wyolum/ultim8x8/kicad/ultim8x8_data/adafruit_products_M0_2796_pinout_v1_0.png

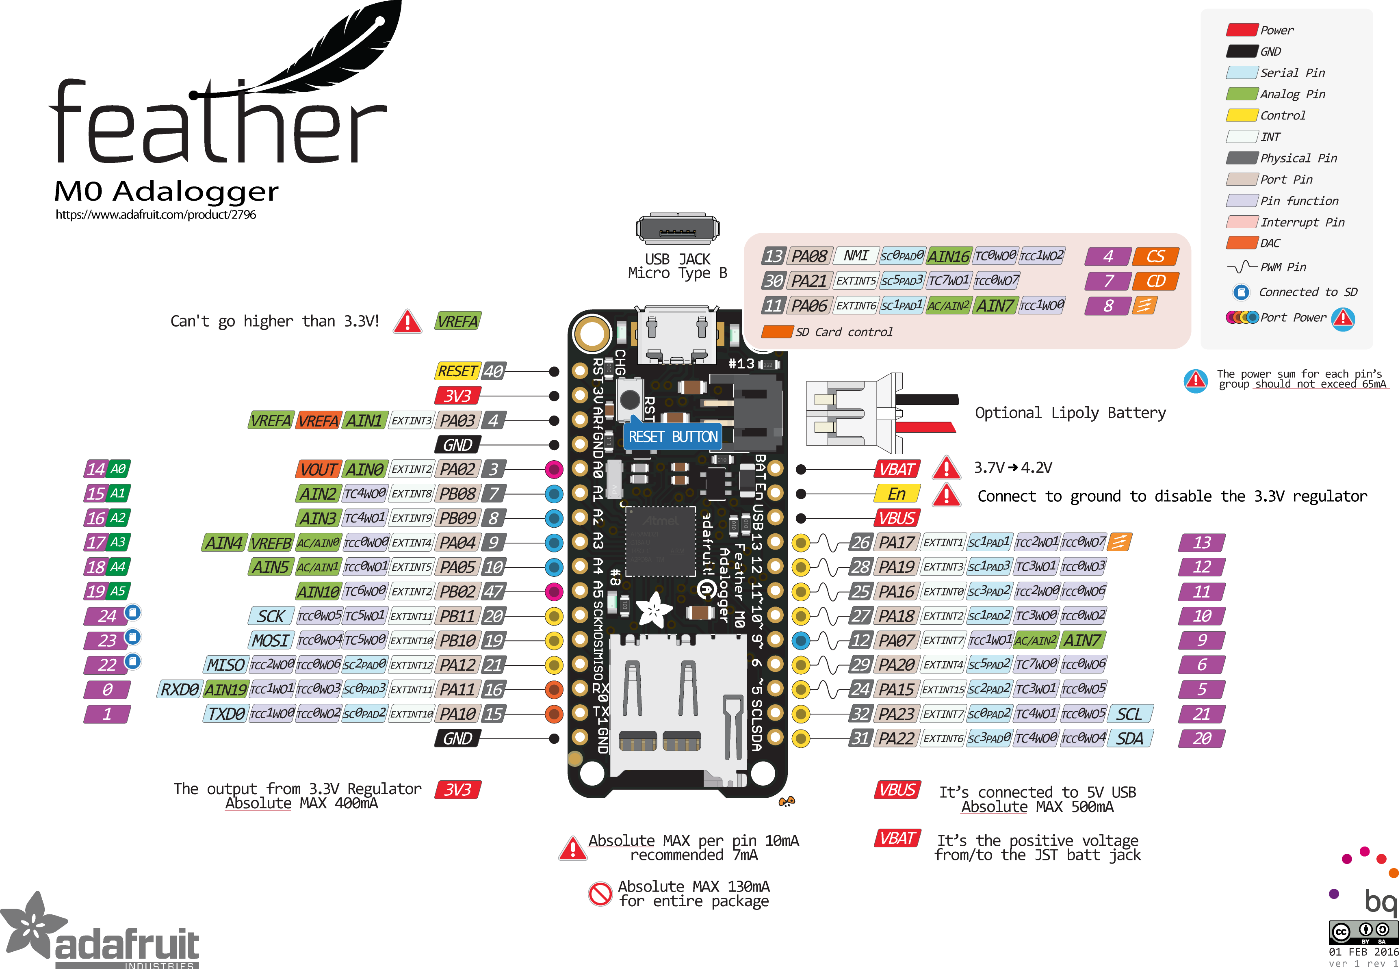
kicad/ultim8x8_data/adafruit_products_M0_2796_pinout_v1_0.png
