wyolum/ultim8x8/kicad/ultim8x8_data/wyolum_butterfly.png

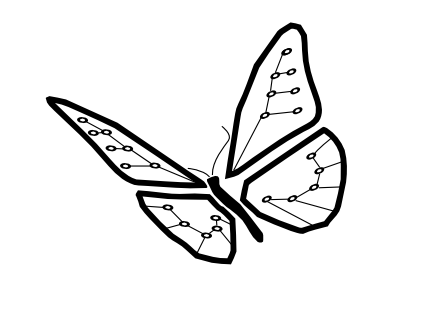
kicad/ultim8x8_data/wyolum_butterfly.png
