wyolum/ultim8x8/kicad/ultim_8x8_v2/ultim8x8_images/ultim8x8_06.png

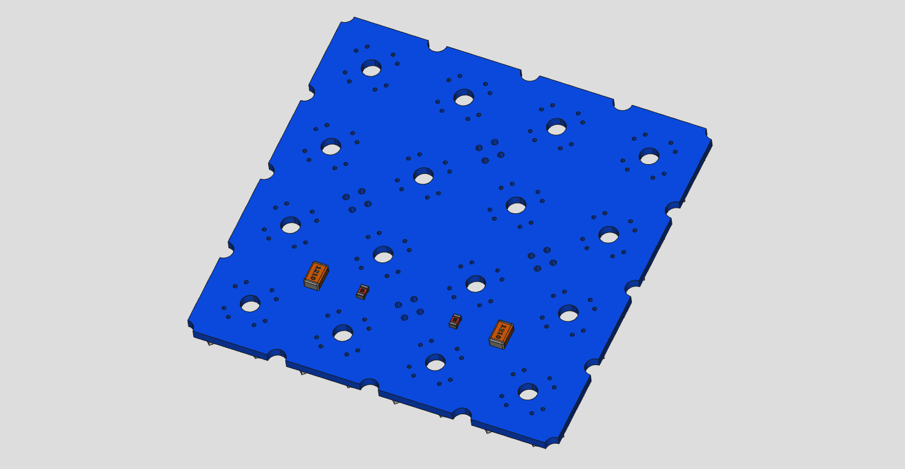
kicad/ultim_8x8_v2/ultim8x8_images/ultim8x8_06.png
