wyolum/ultim8x8/kicad/ultim_8x8_v2/ultim8x8_images/v1/ultim8x8_01.png

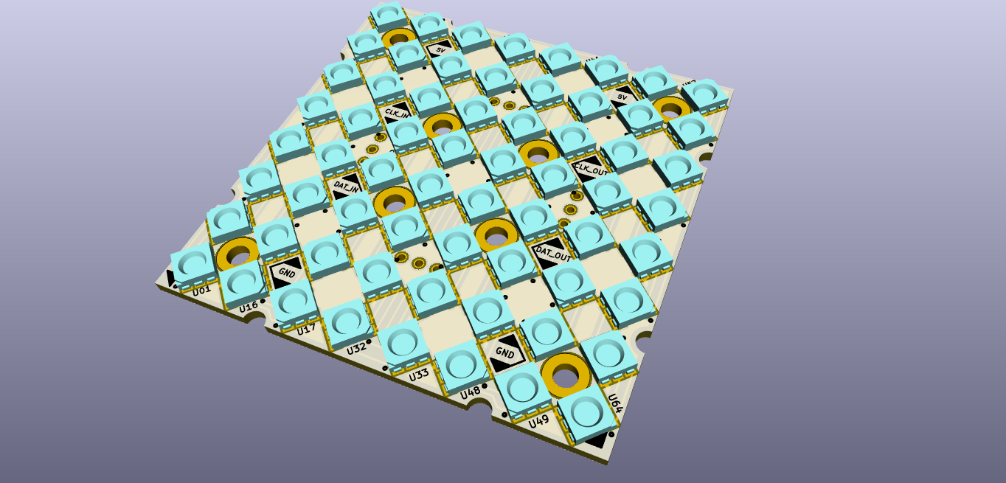
kicad/ultim_8x8_v2/ultim8x8_images/v1/ultim8x8_01.png
