wyolum/ultim8x8/kicad/ultim_bus_conn/ultim_bus_conn_images/ultim_bus_conn_02.png

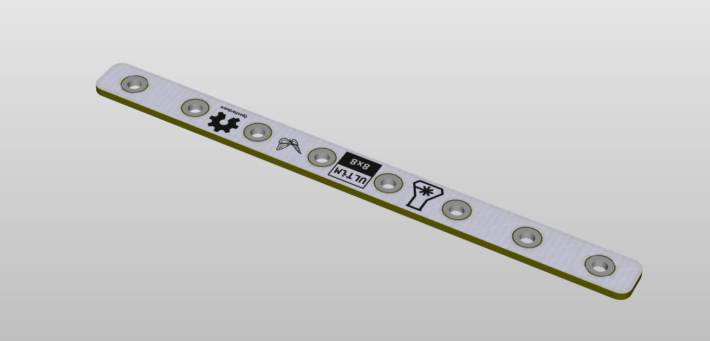
kicad/ultim_bus_conn/ultim_bus_conn_images/ultim_bus_conn_02.png
