wyolum/ultim8x8/arduino/DullesNavKey/enclosure/mouting_guide.stl

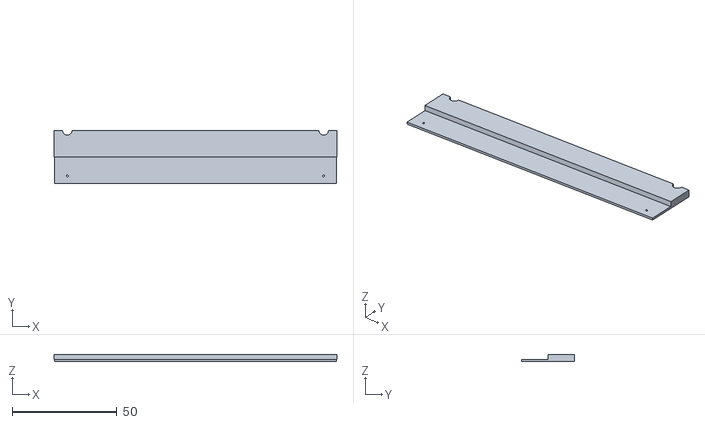
[picture p50: CAD file, 2019-09-12]
arduino/DullesNavKey/enclosure/mouting_guide.stl
135.1 x 25.4 x 3.50
