wyolum/ultim8x8/fabricate/buckle/ultim8x8_feather_buckle_v3.stl

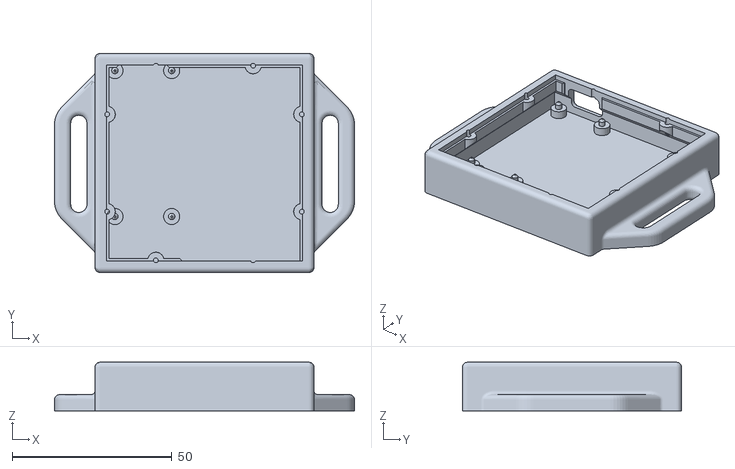
[picture p51: CAD file, 2016-12-25]
fabricate/buckle/ultim8x8_feather_buckle_v3.stl
94.0 x 68.6 x 15.2
