wyolum/ultim8x8/fabricate/STFU/STFU_top.stl

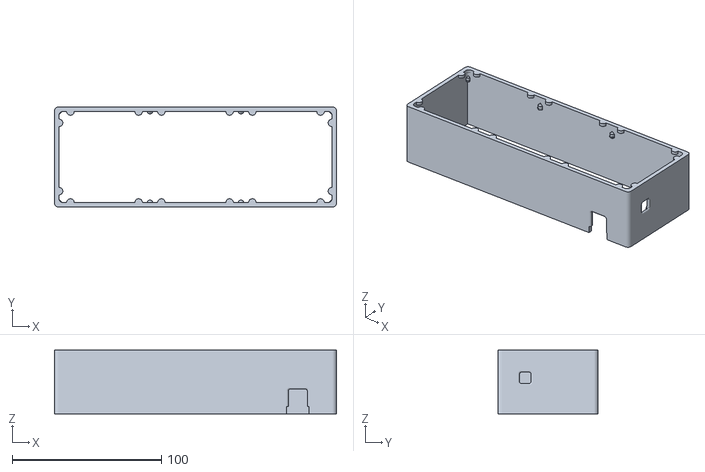
[picture p52: CAD file, 2017-09-21]
fabricate/STFU/STFU_top.stl
189.0 x 67.1 x 42.7
