wyolum/ultim8x8/fabricate/ultim8x_cube01/ultim8x8_cube_face_01.fcstd

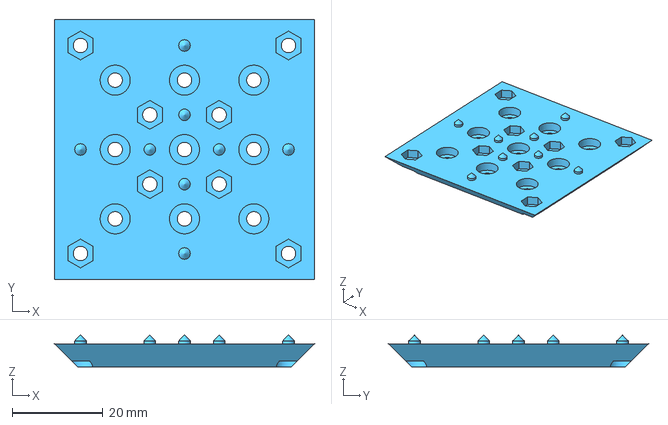
[picture p53: CAD file, 2016-09-29]
fabricate/ultim8x_cube01/ultim8x8_cube_face_01.fcstd
57.1 x 57.1 x 6.99 mm
