wyolum/ultim8x8/fabricate/ultim8x_cube02/cube02_innerface.stl

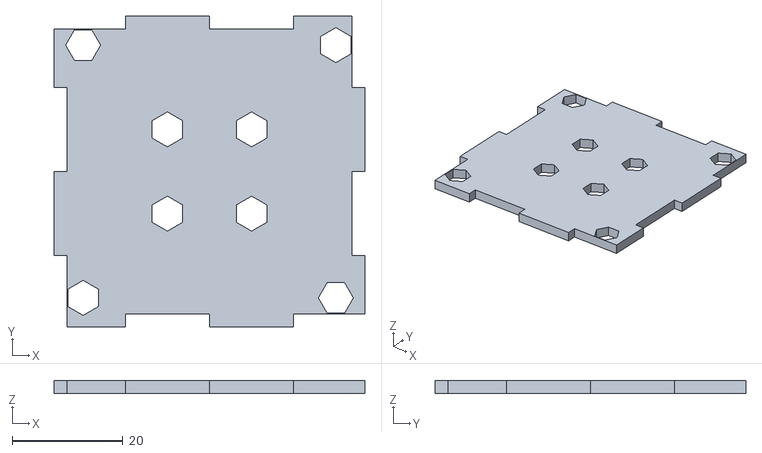
[picture p54: CAD file, 2017-04-09]
fabricate/ultim8x_cube02/cube02_innerface.stl
56.3 x 56.3 x 2.35
