wyolum/ultim8x8/kicad/ultim_8x8_v2/ultim8x8_3D_modules/LED_SMD_APA102_02.step

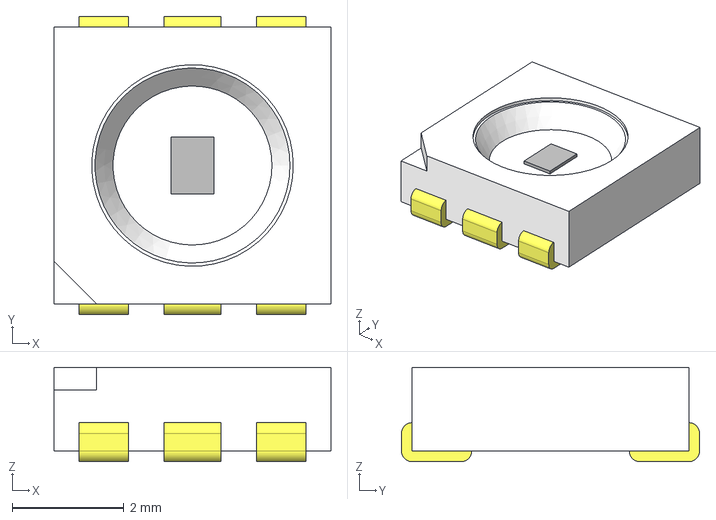
[picture p55: CAD file, 2017-01-15]
kicad/ultim_8x8_v2/ultim8x8_3D_modules/LED_SMD_APA102_02.step
4.95 x 5.33 x 1.69 mm
