wyolum/ultim8x8/kicad/ultim_bus_v5/ultim_bus.FCStd

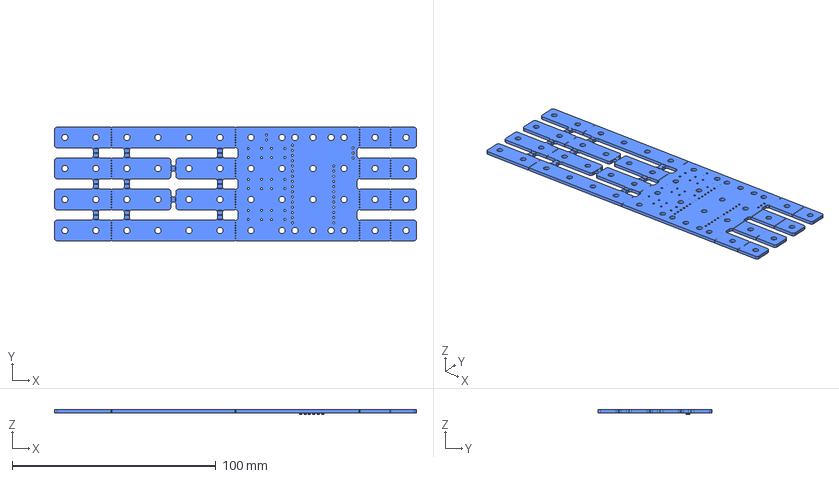
[picture p56: CAD file, 2017-08-31]
kicad/ultim_bus_v5/ultim_bus.FCStd
177.8 x 55.9 x 2.38 mm
Pcb
SW3dPS-0805_SMD_Resistor_
SW3dPS-0805_SMD_Resistor_001
SW3dPS-0805_SMD_Resistor_002
SW3dPS-0805_SMD_Resistor_003
SW3dPS-0805_SMD_Resistor_004
SW3dPS-0805_SMD_Resistor_005
