wyolum/ultim8x8/kicad/ultim_bus_v5/ultim_bus_3dmodules/cap_elco_R100_D200_H460.step

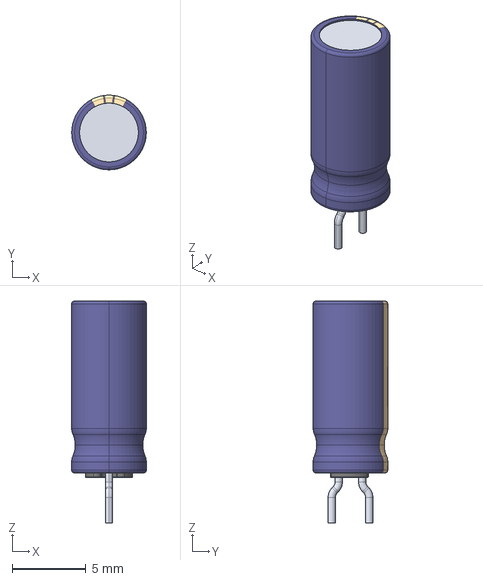
[picture p57: CAD file, 2017-06-14]
kicad/ultim_bus_v5/ultim_bus_3dmodules/cap_elco_R100_D200_H460.step
5.08 x 5.08 x 15.1 mm
