wyolum/ultim8x8/arduino/DullesNavKey/enclosure/hanger.FCStd

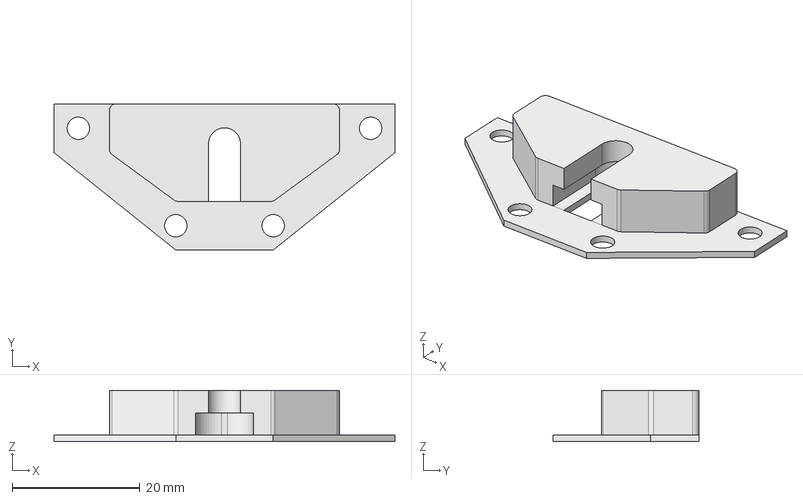
[picture p58: CAD file, 2019-09-02]
arduino/DullesNavKey/enclosure/hanger.FCStd
53.3 x 22.9 x 8.00 mm
