wyolum/ultim8x8/fabricate/STFU/STFU_acrylic.stl

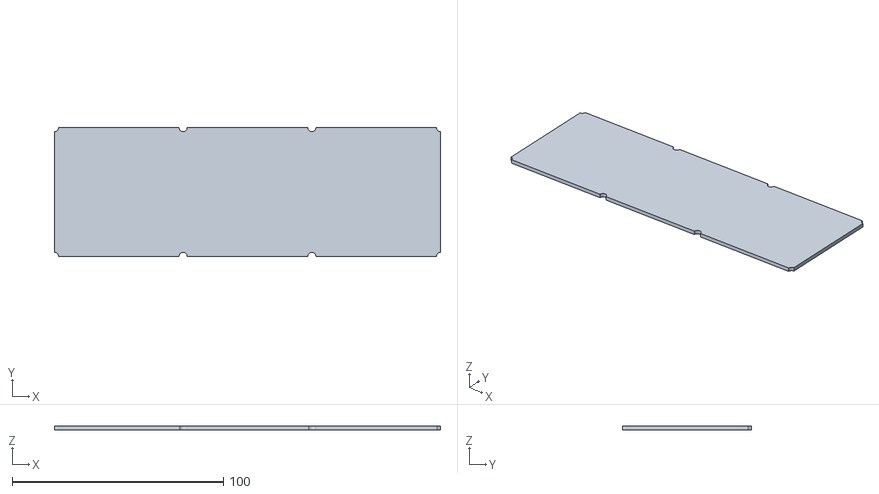
[picture p59: CAD file, 2017-09-21]
fabricate/STFU/STFU_acrylic.stl
182.9 x 61.0 x 2.03
