wyolum/ultim8x8/kicad/ultim_bus_v5/ultim_bus_3dmodules/SW_Switch_SPDT.step

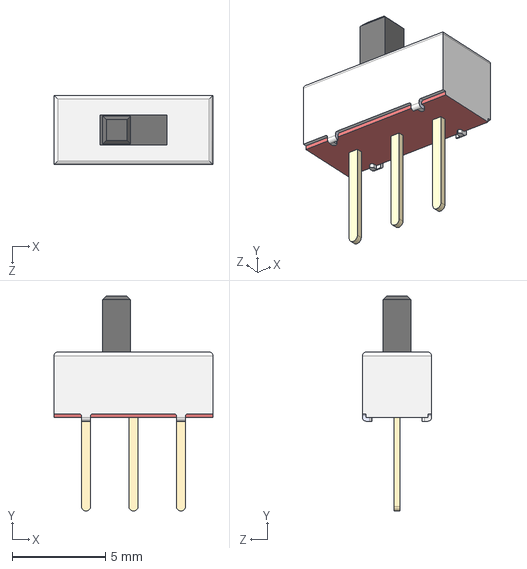
[picture p60: CAD file, 2017-06-14]
kicad/ultim_bus_v5/ultim_bus_3dmodules/SW_Switch_SPDT.step
8.50 x 11.5 x 3.70 mm
