wyolum/ultim8x8/arduino/DesKlok/ClockIOT.stl

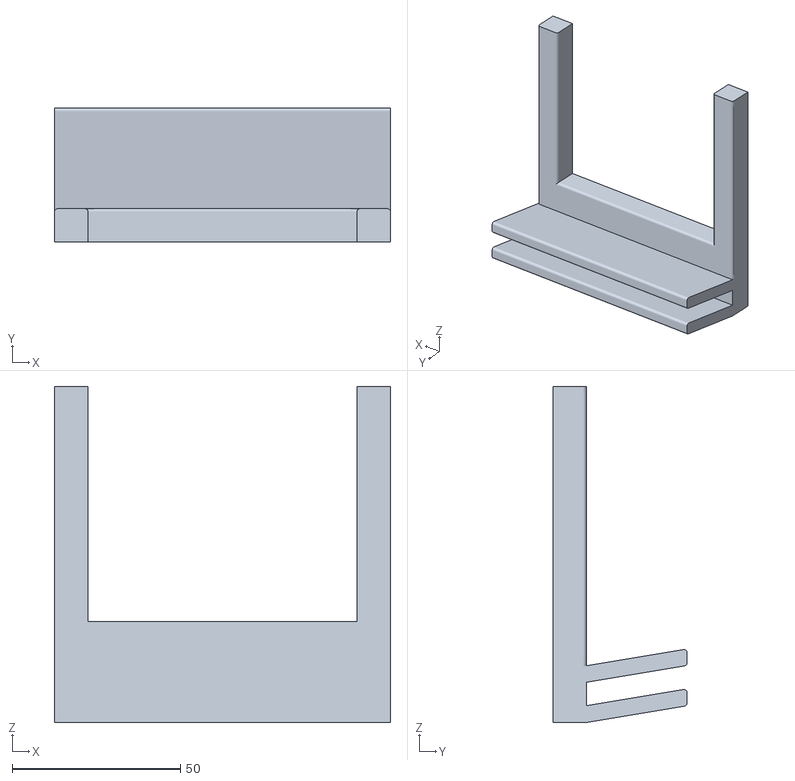
[picture p61: CAD file, 2022-12-24]
arduino/DesKlok/ClockIOT.stl
100.0 x 40.0 x 100.0
