wyolum/ultim8x8/fabricate/ultim8x_cube02/cube02_outerface.stl

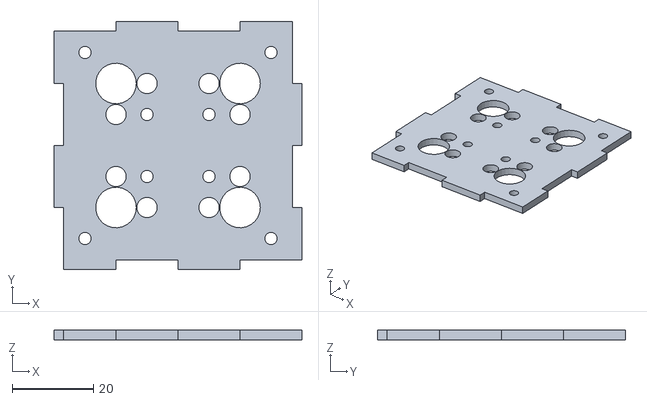
[picture p62: CAD file, 2017-04-09]
fabricate/ultim8x_cube02/cube02_outerface.stl
61.0 x 61.0 x 2.35
