wyolum/ultim8x8/kicad/ultim_bus_v5/ultim_bus_3dmodules/SW_slide_eg1270.step

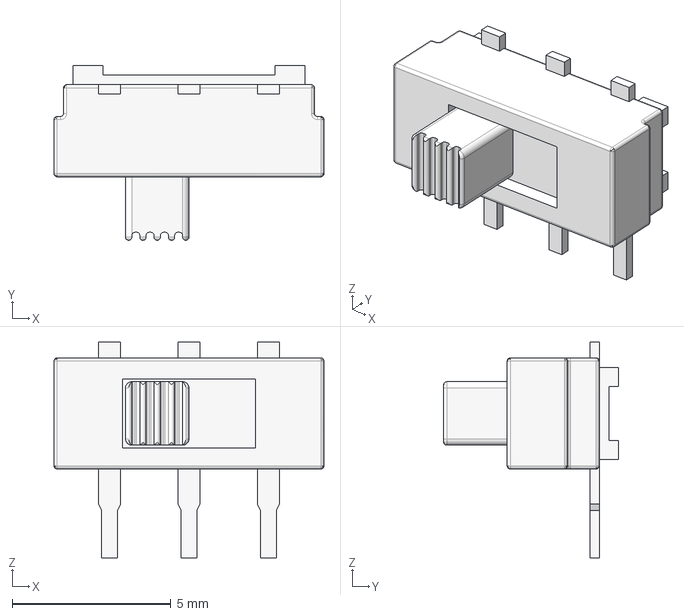
[picture p64: CAD file, 2017-06-14]
kicad/ultim_bus_v5/ultim_bus_3dmodules/SW_slide_eg1270.step
8.50 x 5.50 x 6.80 mm
