wyolum/ultim8x8/fabricate/ultim8x_cube02/cube02_oneface_combined.stl

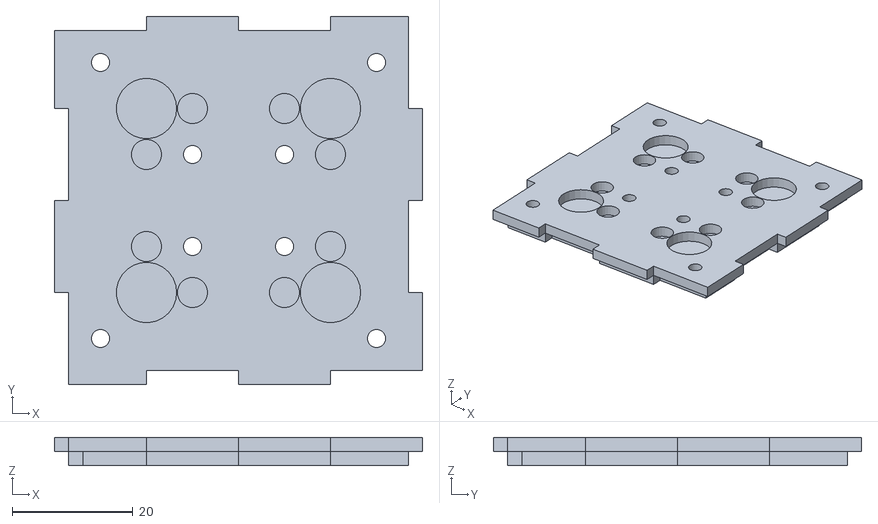
[picture p65: CAD file, 2017-04-09]
fabricate/ultim8x_cube02/cube02_oneface_combined.stl
61.0 x 61.0 x 4.70
