wyolum/ultim8x8/kicad/ultim_8x8_v2/ultim8x8_3D_modules/socket_ra_4pin.step

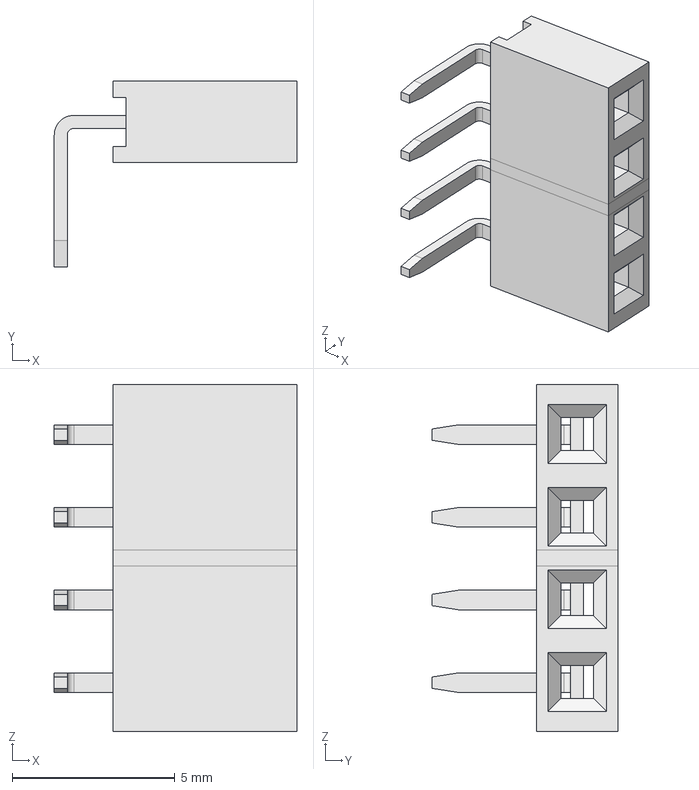
[picture p66: CAD file, 2016-09-08]
kicad/ultim_8x8_v2/ultim8x8_3D_modules/socket_ra_4pin.step
7.45 x 5.70 x 10.7 mm
