wyolum/ultim8x8/kicad/ultim_bus_v5/ultim_bus_3dmodules/r_0805.step

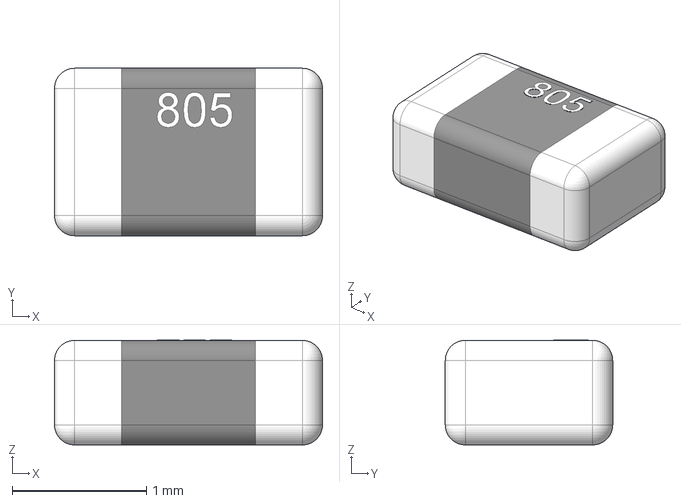
[picture p67: CAD file, 2017-04-03]
kicad/ultim_bus_v5/ultim_bus_3dmodules/r_0805.step
2.00 x 1.25 x 0.782 mm
