wyolum/ultim8x8/kicad/ultim_8x8_v2/ultim8x8_3D_modules/header_1x3_TH_2_54mm.step

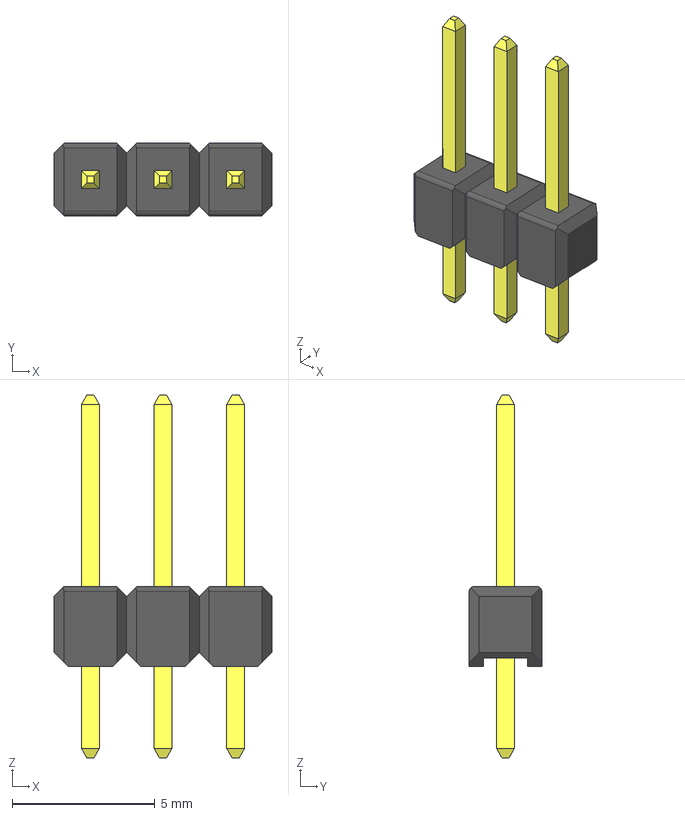
[picture p68: CAD file, 2016-03-18]
kicad/ultim_8x8_v2/ultim8x8_3D_modules/header_1x3_TH_2_54mm.step
7.62 x 2.54 x 12.7 mm
