wyolum/ultim8x8/kicad/ultim_8x8_v2/ultim8x8_3D_modules/cap_1210_3225M.step

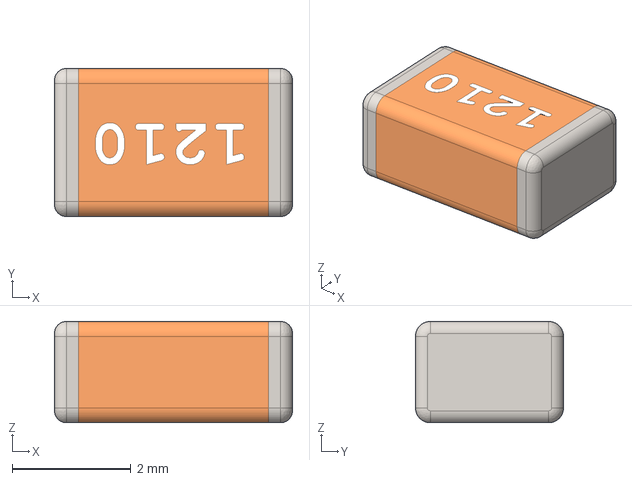
[picture p69: CAD file, 2016-03-18]
kicad/ultim_8x8_v2/ultim8x8_3D_modules/cap_1210_3225M.step
4.00 x 2.49 x 1.70 mm
