wyolum/ultim8x8/kicad/ultim_8x8_v2/ultim8x8_3D_modules/Cap_0805_2012.step

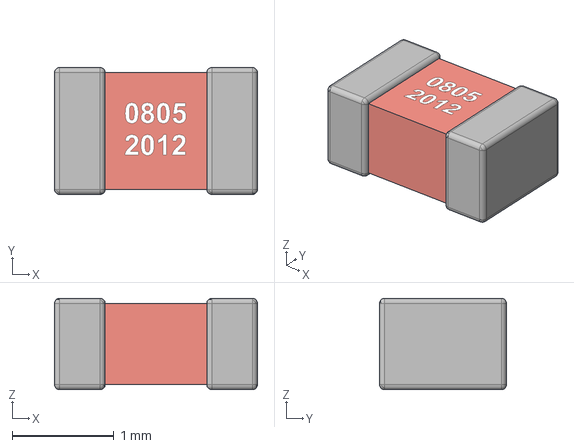
[picture p70: CAD file, 2016-02-18]
kicad/ultim_8x8_v2/ultim8x8_3D_modules/Cap_0805_2012.step
2.00 x 1.25 x 0.9 mm
