wyolum/ultim8x8/kicad/ultim_8x8_v2/ultim8x8_3D_modules/header_Male_RA_Low_3Pin.step

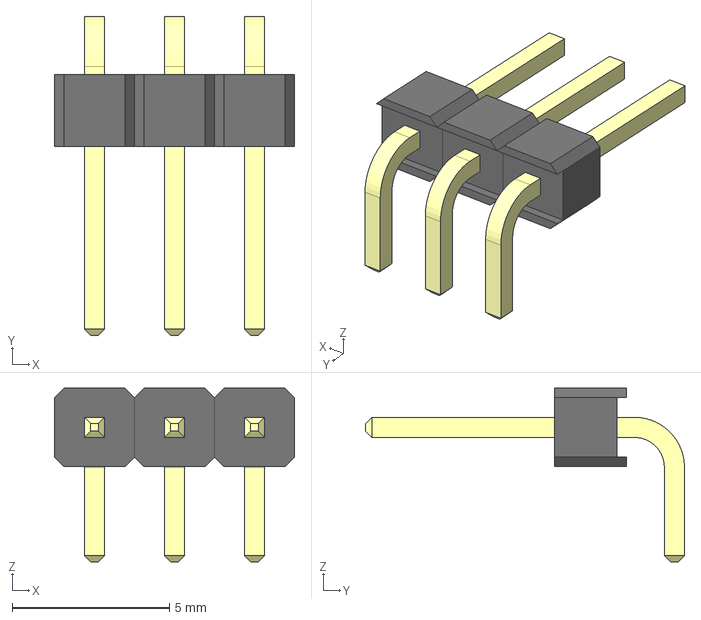
[picture p71: CAD file, 2016-02-18]
kicad/ultim_8x8_v2/ultim8x8_3D_modules/header_Male_RA_Low_3Pin.step
7.62 x 10.1 x 5.52 mm
