wyolum/ultim8x8/fabricate/STFU/SFTU01.png

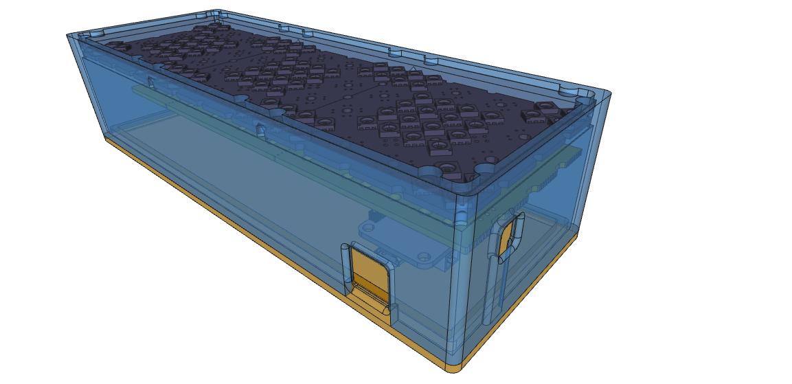
fabricate/STFU/SFTU01.png
