wyolum/ultim8x8/fabricate/STFU/STFU02.png

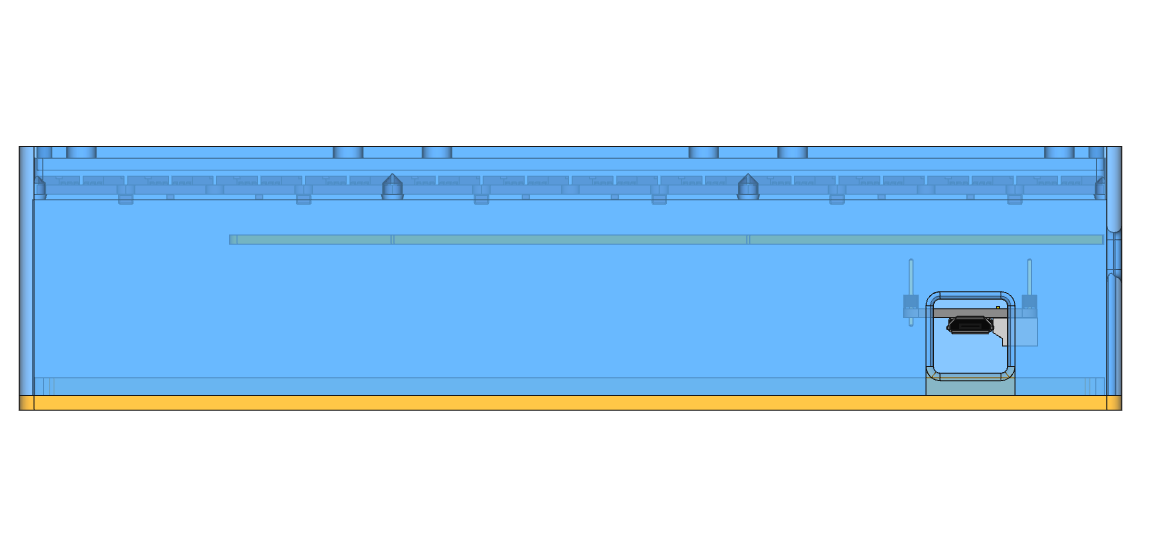
fabricate/STFU/STFU02.png
