wyolum/ultim8x8/fabricate/STFU/STFU03.png

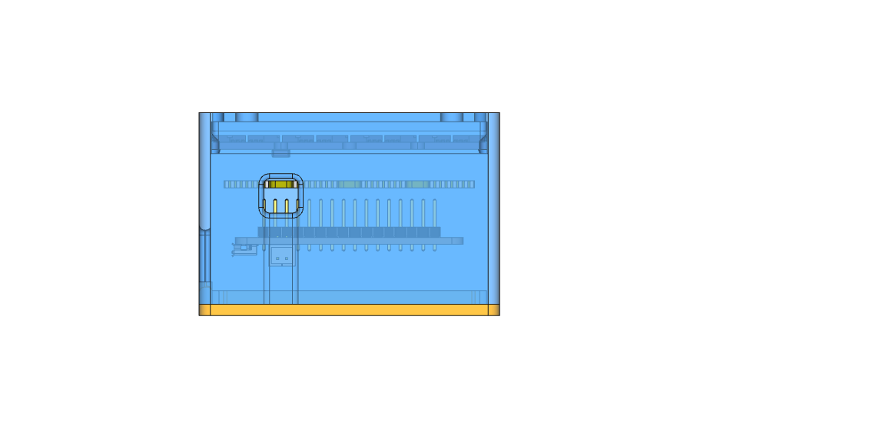
fabricate/STFU/STFU03.png
