wyolum/ultim8x8/fabricate/STFU/STFU04.png

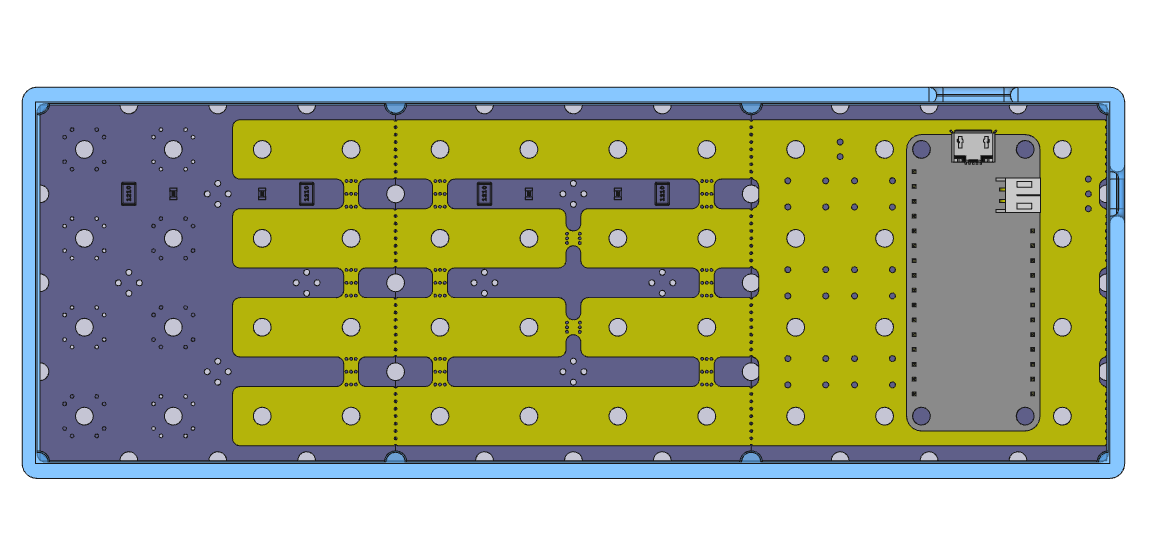
fabricate/STFU/STFU04.png
