wyolum/ultim8x8/fabricate/ultim8x_assy_idea/ultim8x_assy_01.png

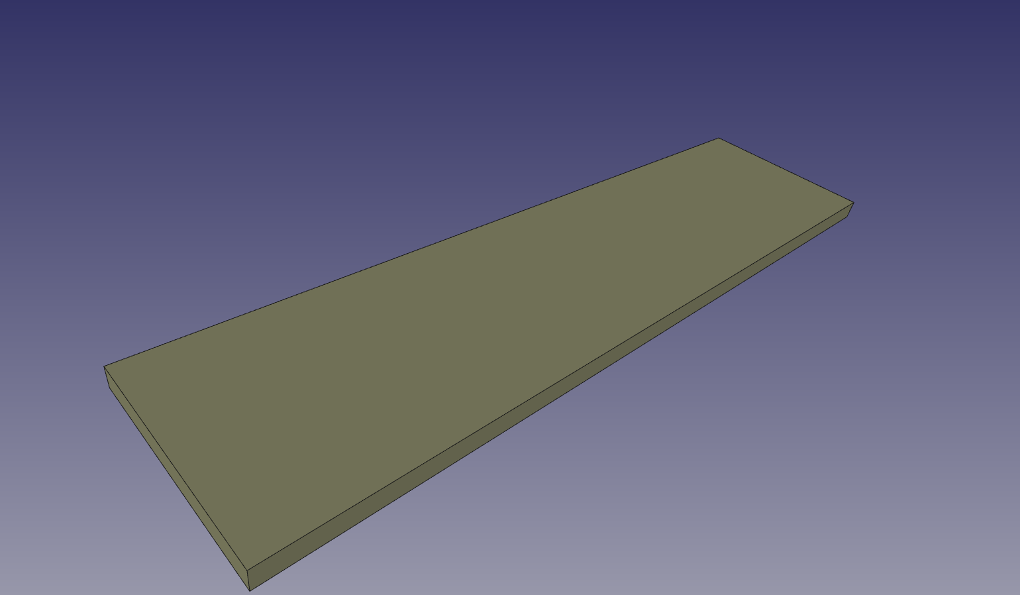
fabricate/ultim8x_assy_idea/ultim8x_assy_01.png
