wyolum/ultim8x8/fabricate/ultim8x_cube01/images/cube01.png

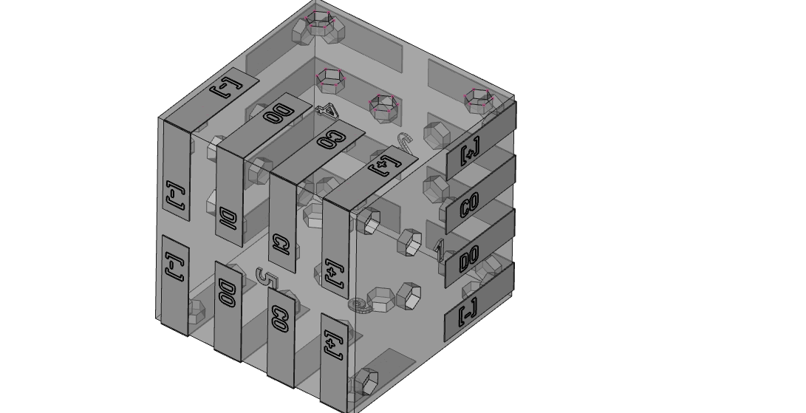
fabricate/ultim8x_cube01/images/cube01.png
