wyolum/ultim8x8/fabricate/ultim8x_cube01/images/cube03.png

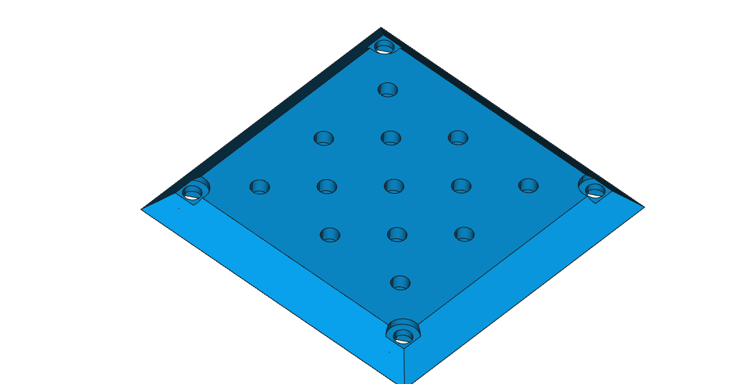
fabricate/ultim8x_cube01/images/cube03.png
