wyolum/ultim8x8/fabricate/ultim8x_cube02/images/cube02_05.png

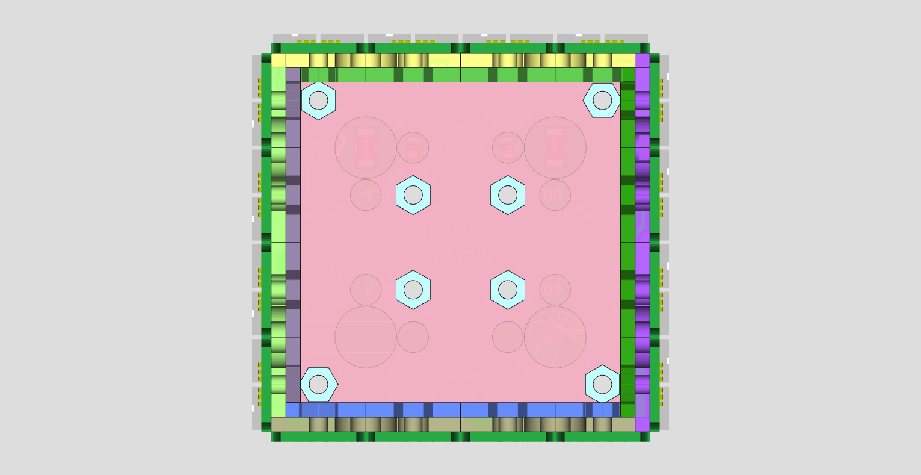
fabricate/ultim8x_cube02/images/cube02_05.png
