wyolum/ultim8x8/kicad/ultim_bus_conn/ultim_bus_conn_pdf/ultim_bus_conn.pdf

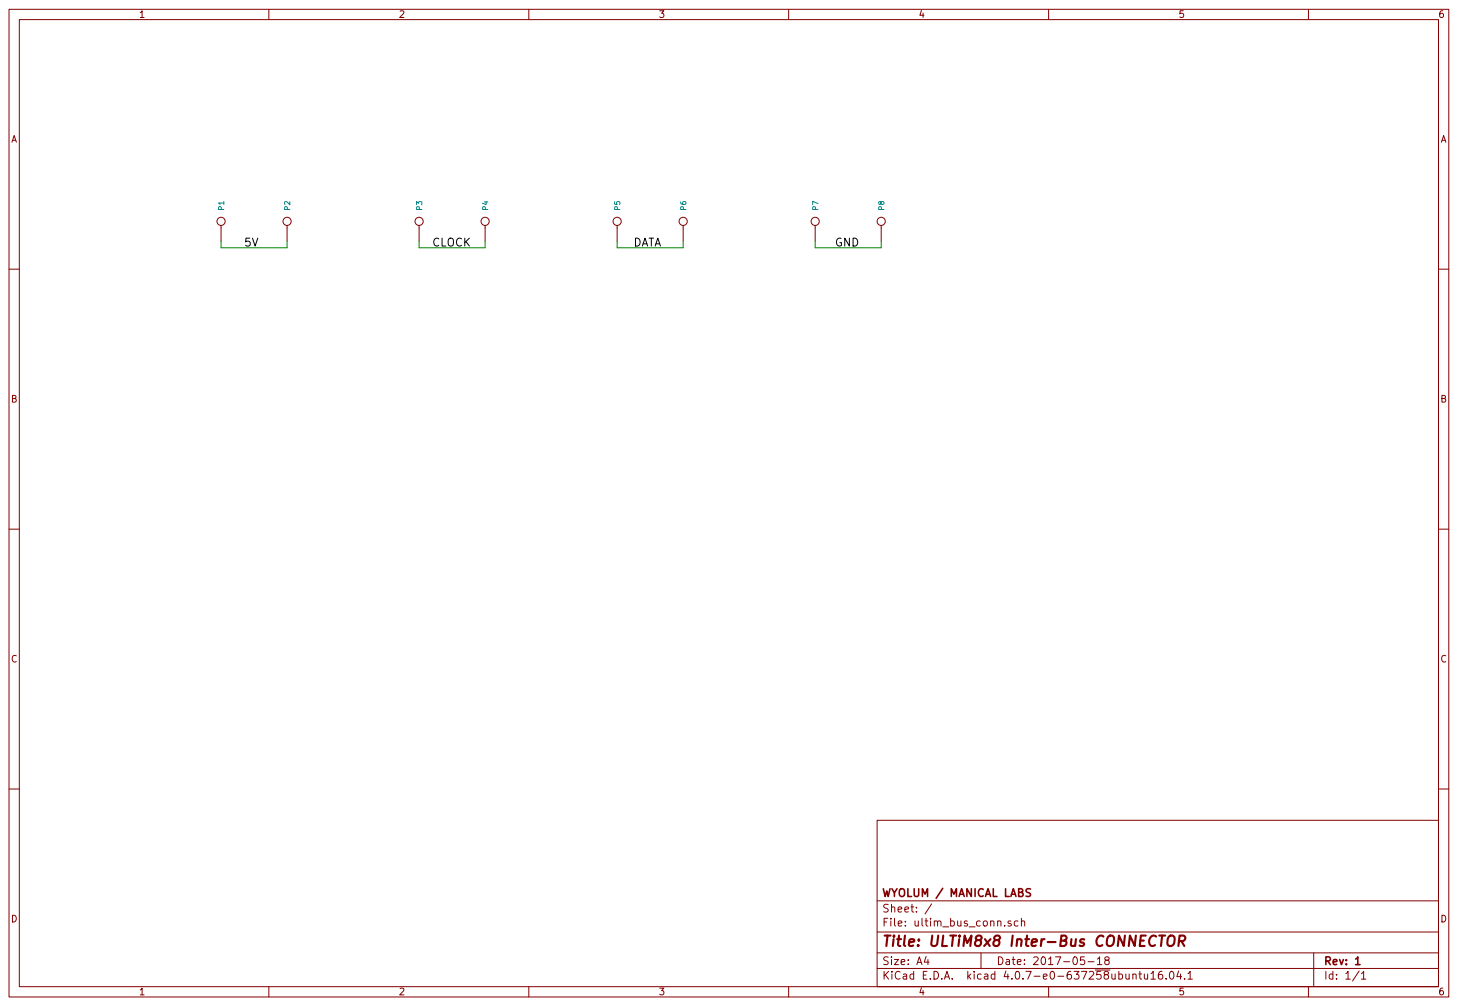
[picture p95: page 1]

Id: 1/1 Title: ULTiM8x8 Inter-Bus CONNECTOR
