wyolum/ultim8x8/kicad/ultim_8x8_v2/ultim8x8_pdf/ultim8x8-B.SilkS.pdf

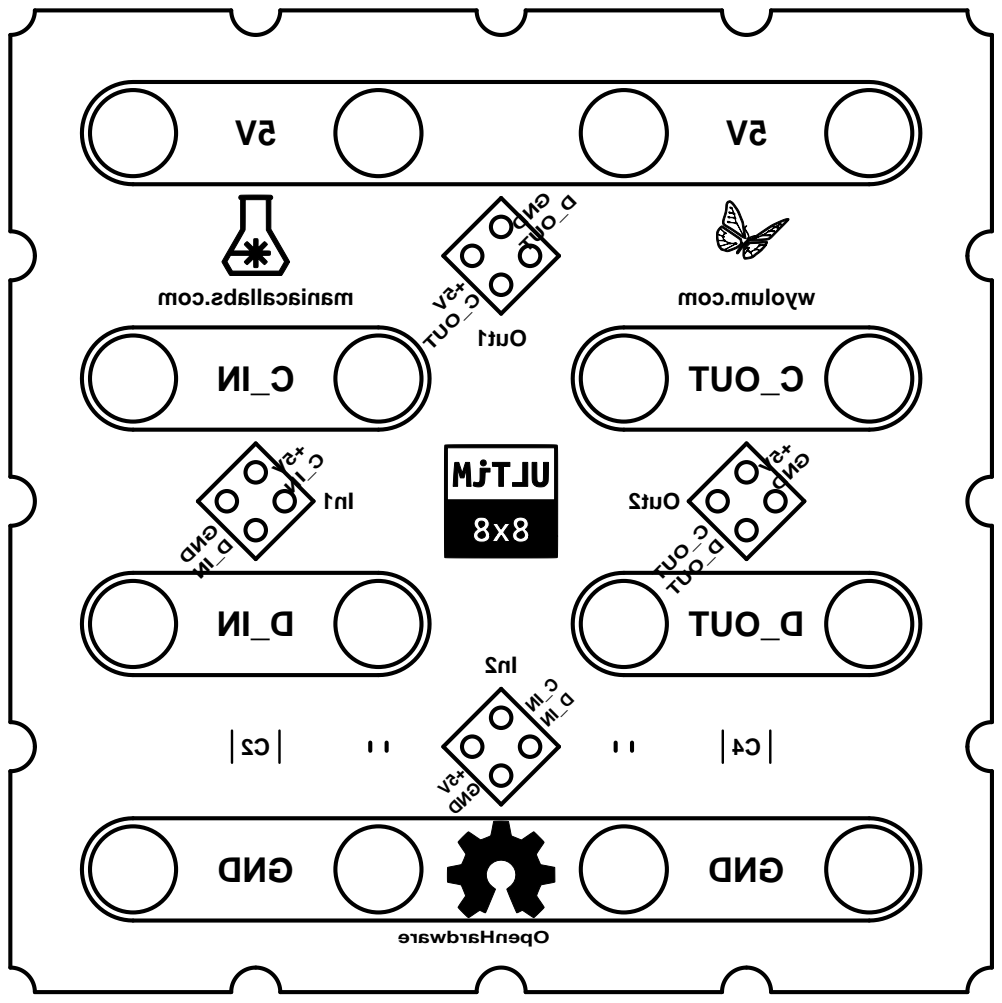
[picture p96: page 1]

File: ultim8x8.kicad_pcb Sheet: WyoManical Labs

Id: 1/1 Title: ultim8x8 RGB LED panel
