wyolum/ultim8x8/kicad/ultim_8x8_v2/ultim8x8_pdf/ultim8x8.pdf

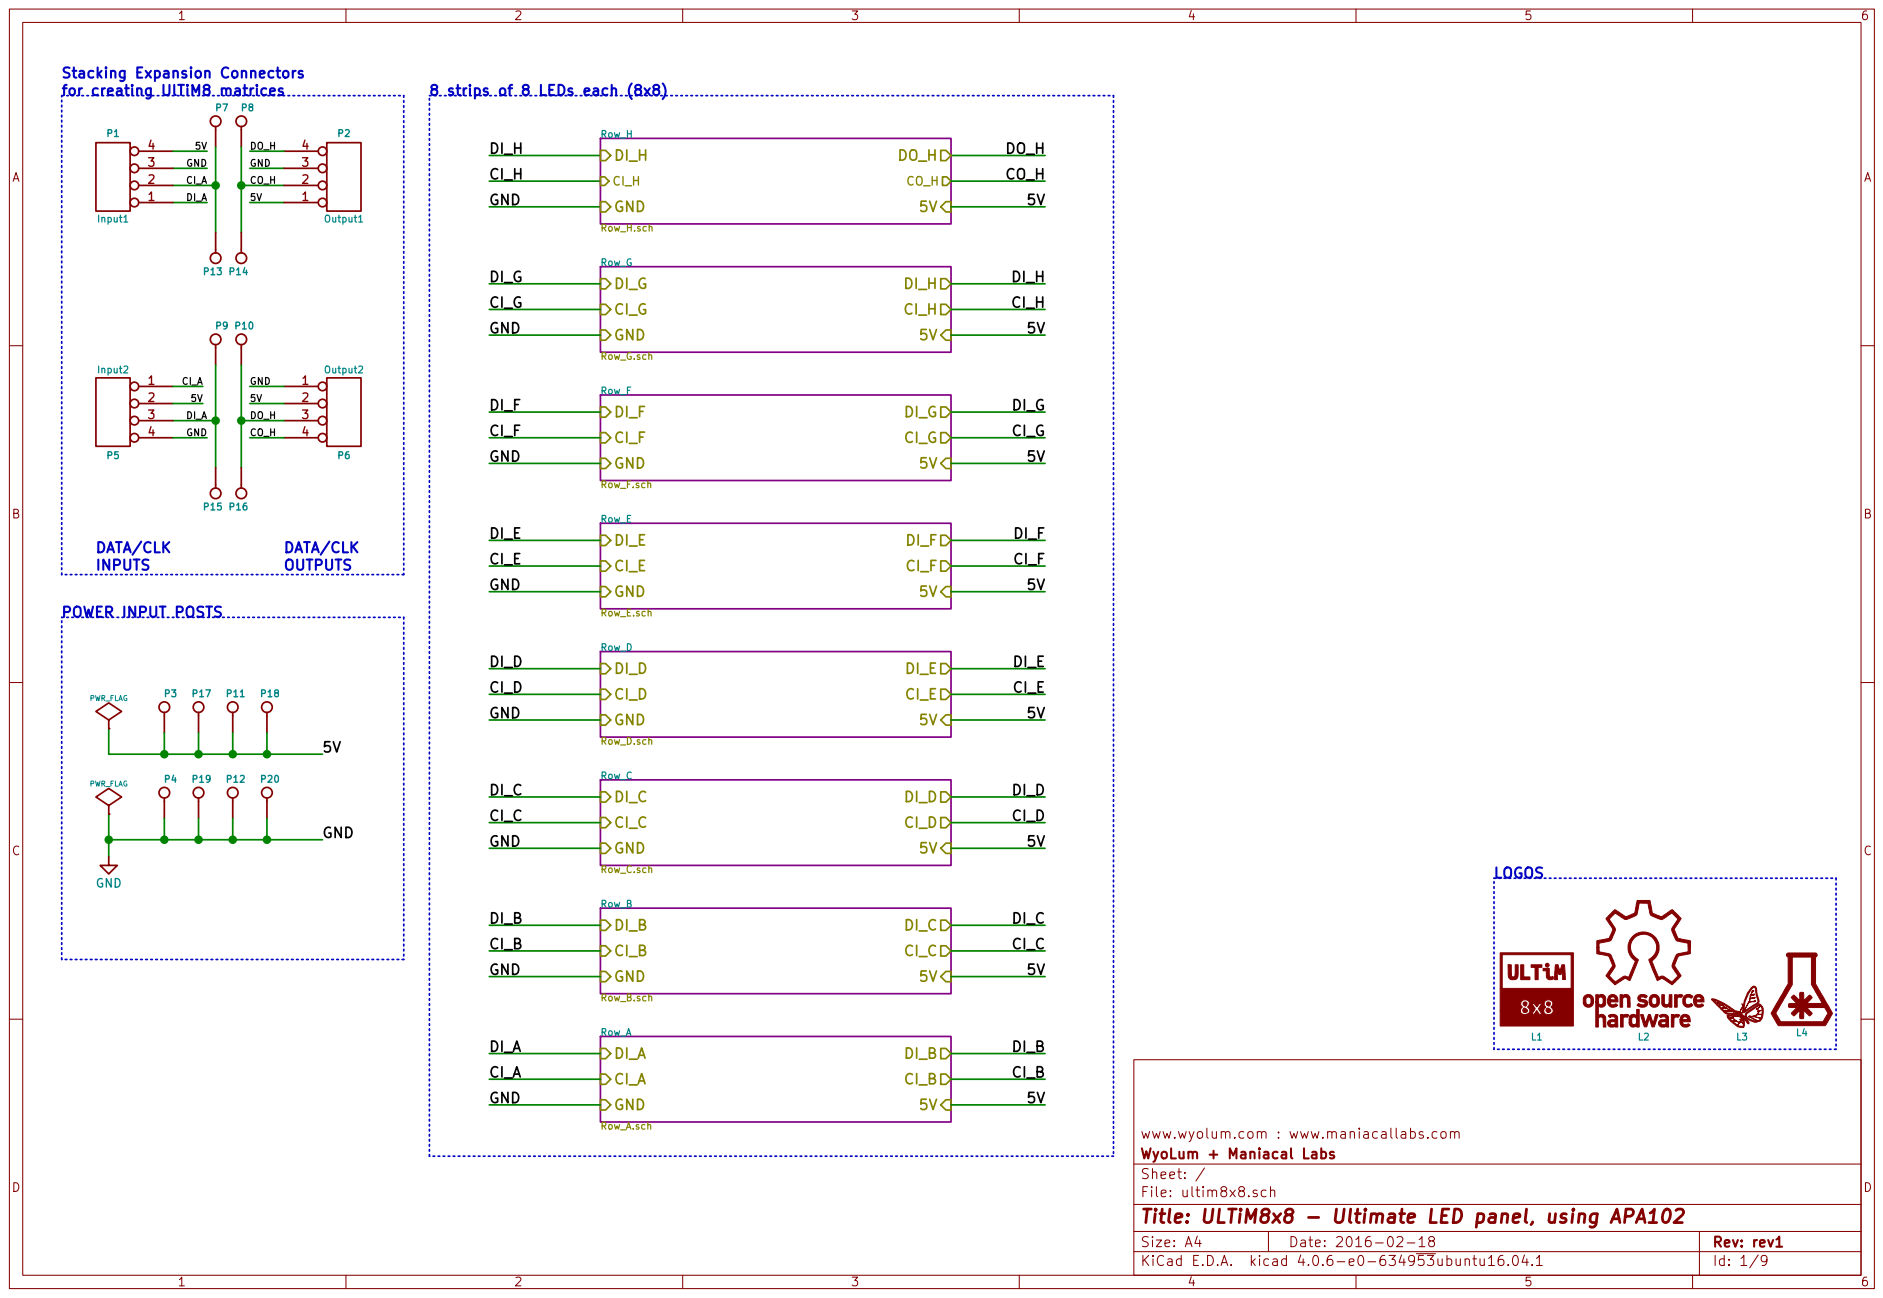
[picture p101: page 1]

8 strips of 8 LEDs each (8x8)

www.wyolum.com : www.maniacallabs.com
File: ultim8x8.sch Sheet: / WyoLum + Maniacal Labs

Id: 1/9 Title: ULTiM8x8 - Ultimate LED panel, using APA102

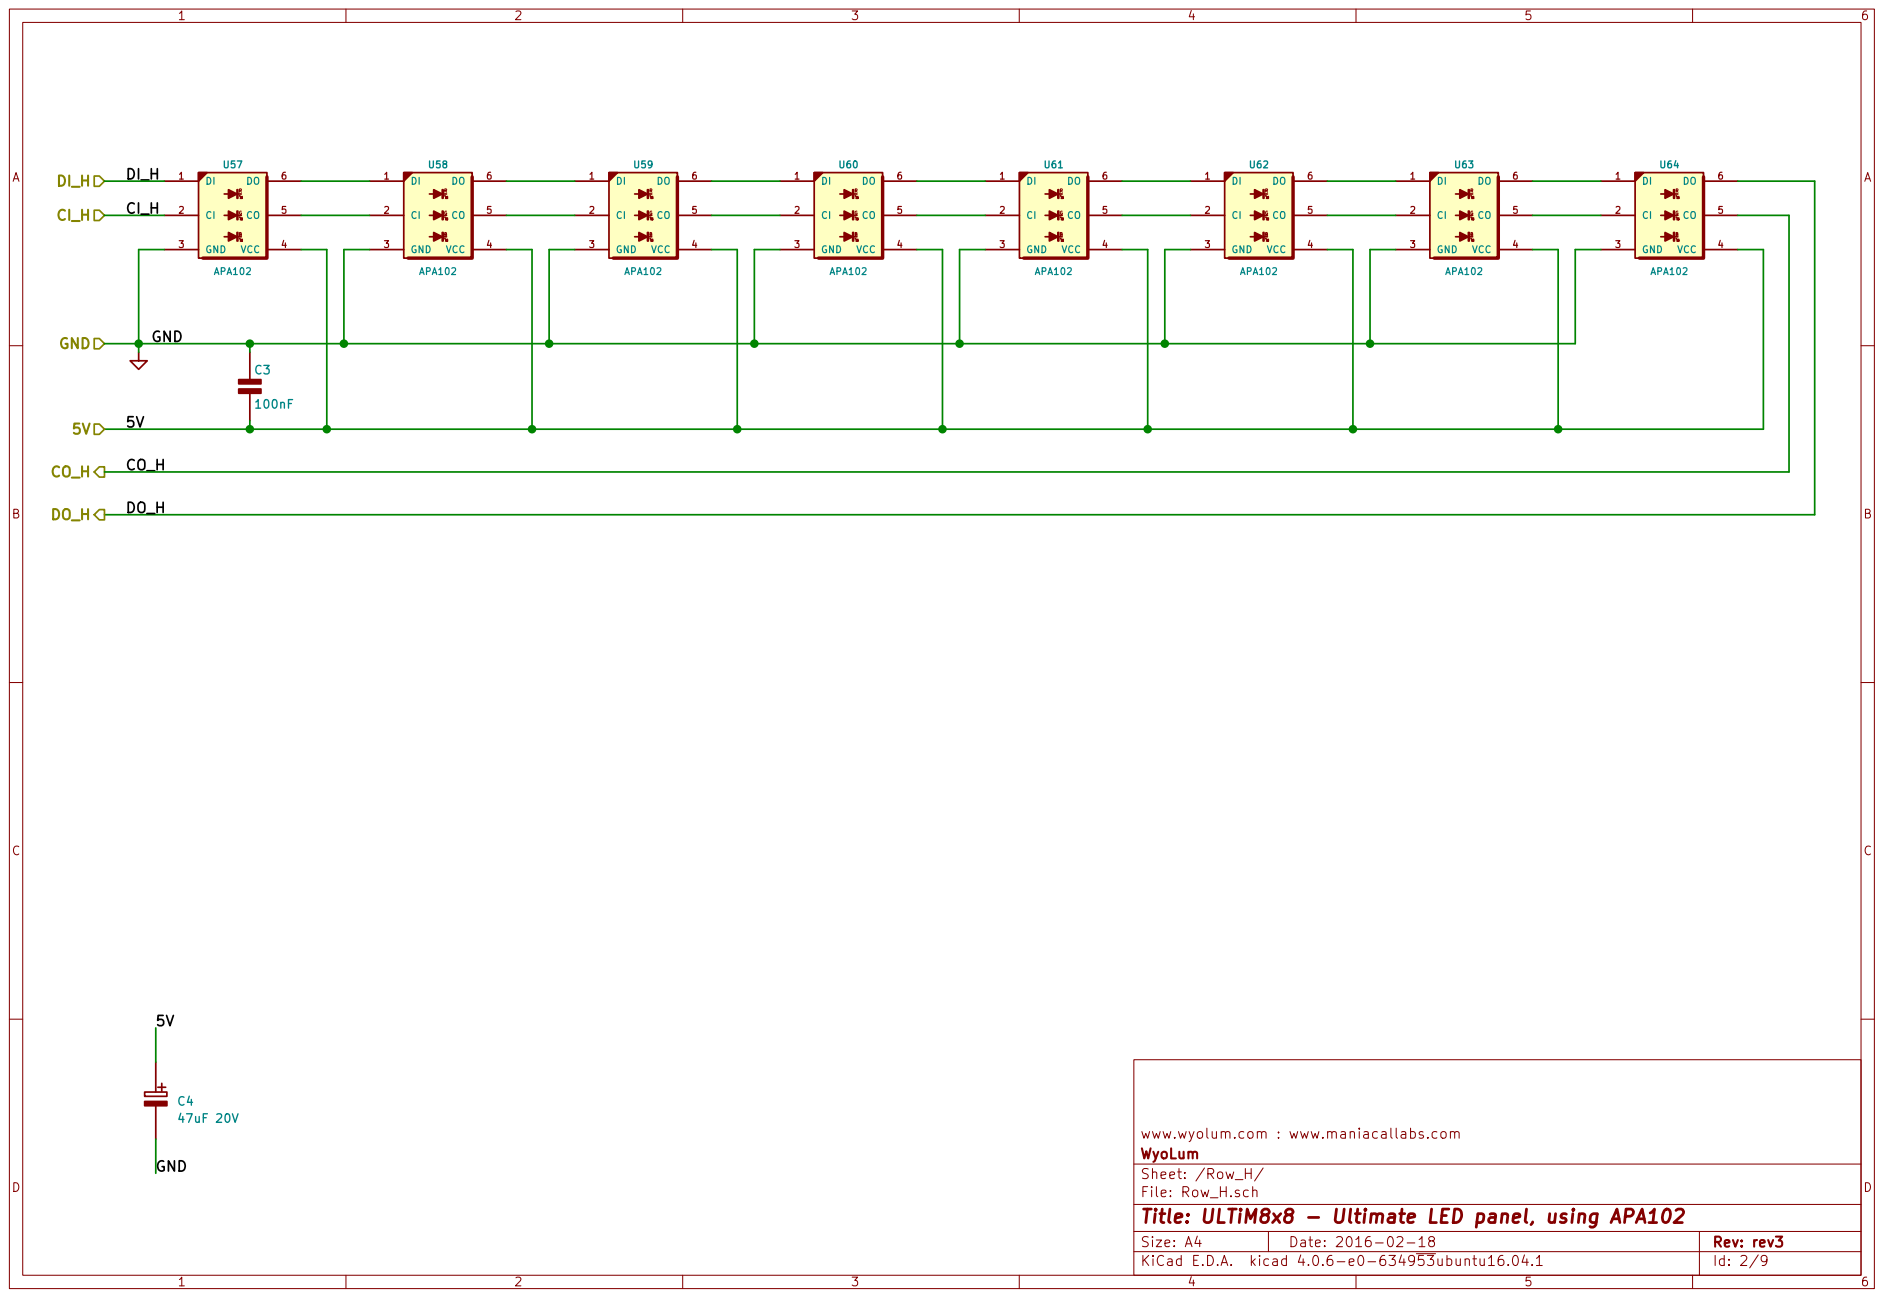
[picture p102: page 2]

www.wyolum.com : www.maniacallabs.com
WyoLum
Sheet: /Row_H/
File: Row_H.sch
Id: 2/9 Title: ULTiM8x8 - Ultimate LED panel, using APA102

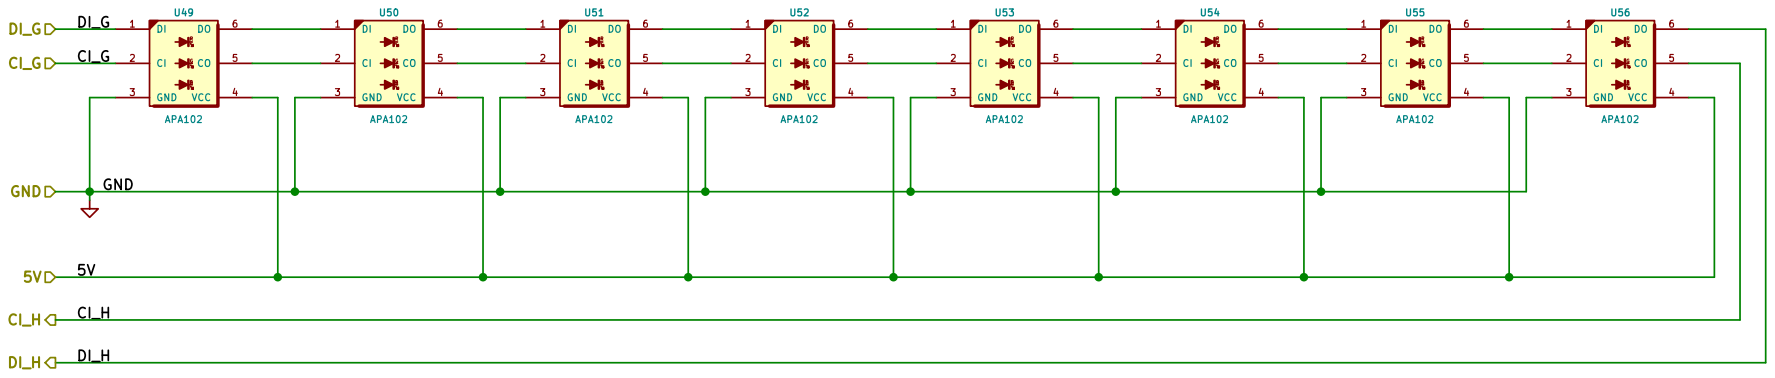
[picture p103: page 3]

www.wyolum.com : www.maniacallabs.com
WyoLum
Sheet: /Row_G/
File: Row_G.sch
Id: 3/9 Title: ULTiM8x8 - Ultimate LED panel, using APA102

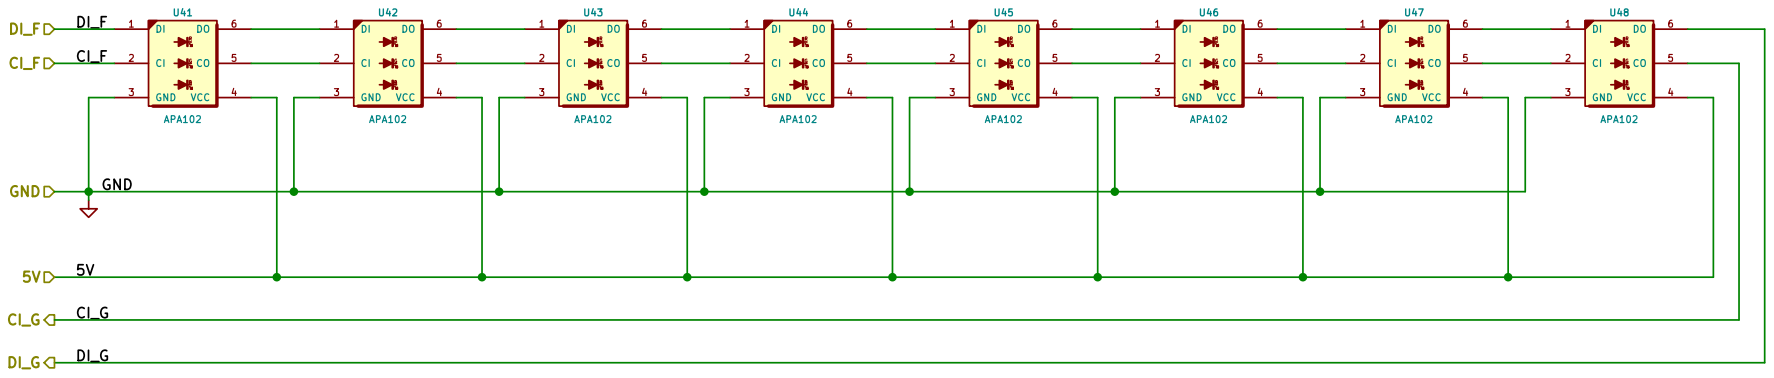
[picture p104: page 4]

www.wyolum.com : www.maniacallabs.com
WyoLum
Sheet: /Row_F/
File: Row_F.sch
Id: 4/9 Title: ULTiM8x8 - Ultimate LED panel, using APA102

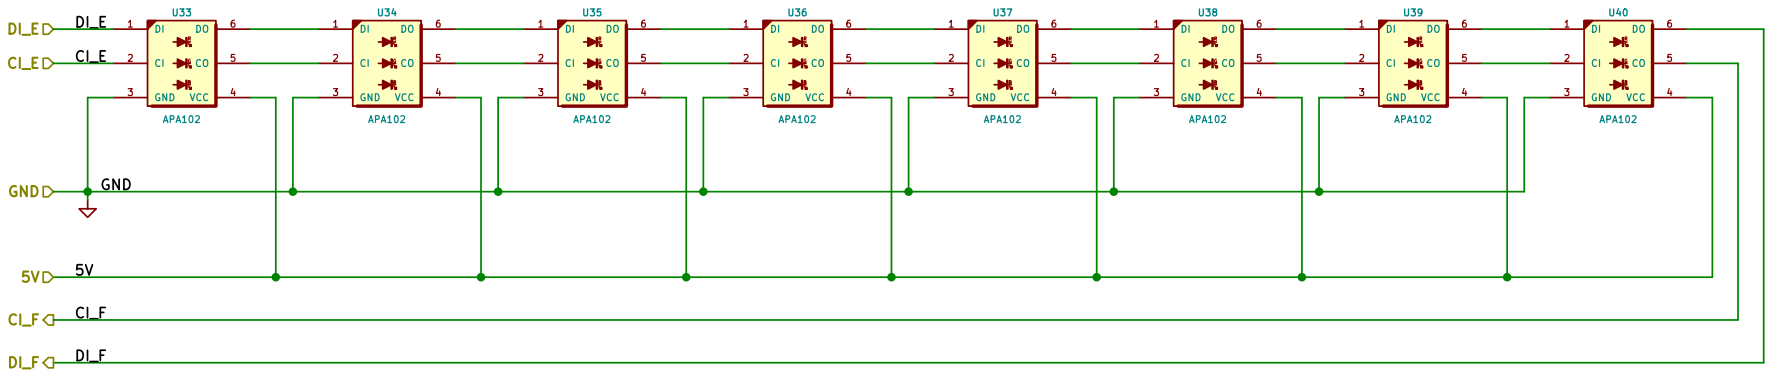
[picture p105: page 5]

www.wyolum.com : www.maniacallabs.com
WyoLum
Sheet: /Row_E/
File: Row_E.sch
Id: 5/9 Title: ULTiM8x8 - Ultimate LED panel, using APA102

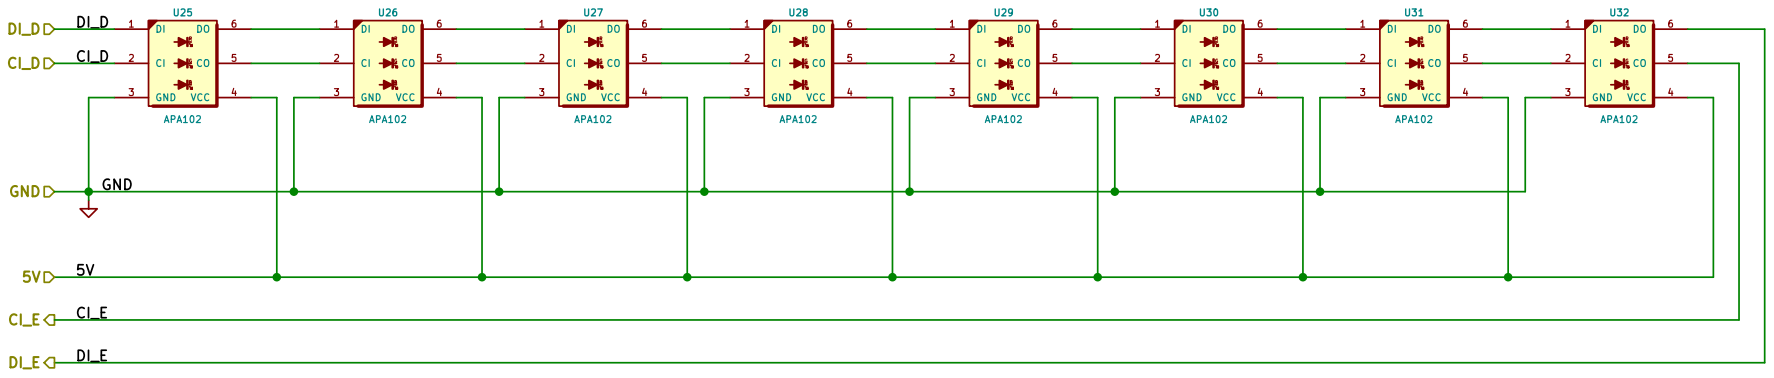
[picture p106: page 6]

www.wyolum.com : www.maniacallabs.com
WyoLum
Sheet: /Row_D/
File: Row_D.sch
Id: 6/9 Title: ULTiM8x8 - Ultimate LED panel, using APA102

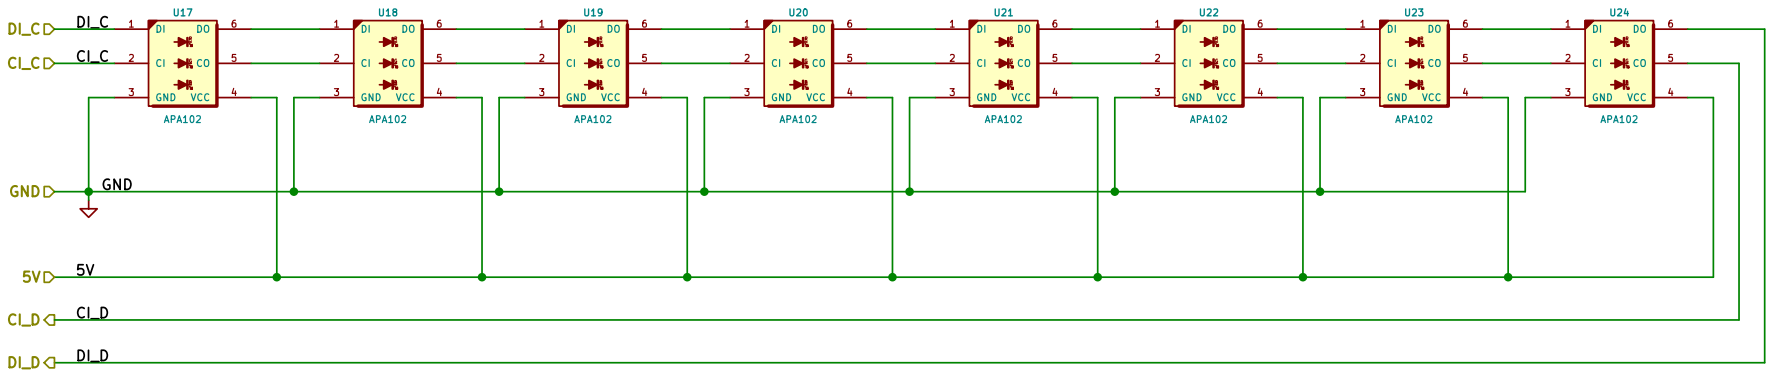
[picture p107: page 7]

www.wyolum.com : www.maniacallabs.com
WyoLum
Sheet: /Row_C/
File: Row_C.sch
Id: 7/9 Title: ULTiM8x8 - Ultimate LED panel, using APA102

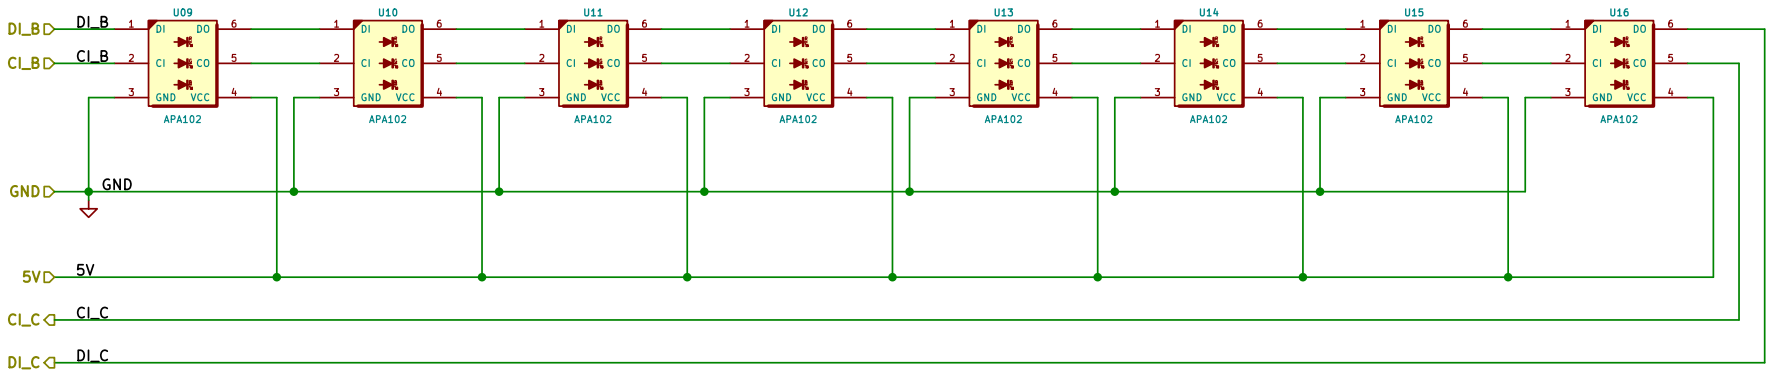
[picture p108: page 8]

www.wyolum.com : www.maniacallabs.com
WyoLum
Sheet: /Row_B/
File: Row_B.sch
Id: 8/9 Title: ULTiM8x8 - Ultimate LED panel, using APA102

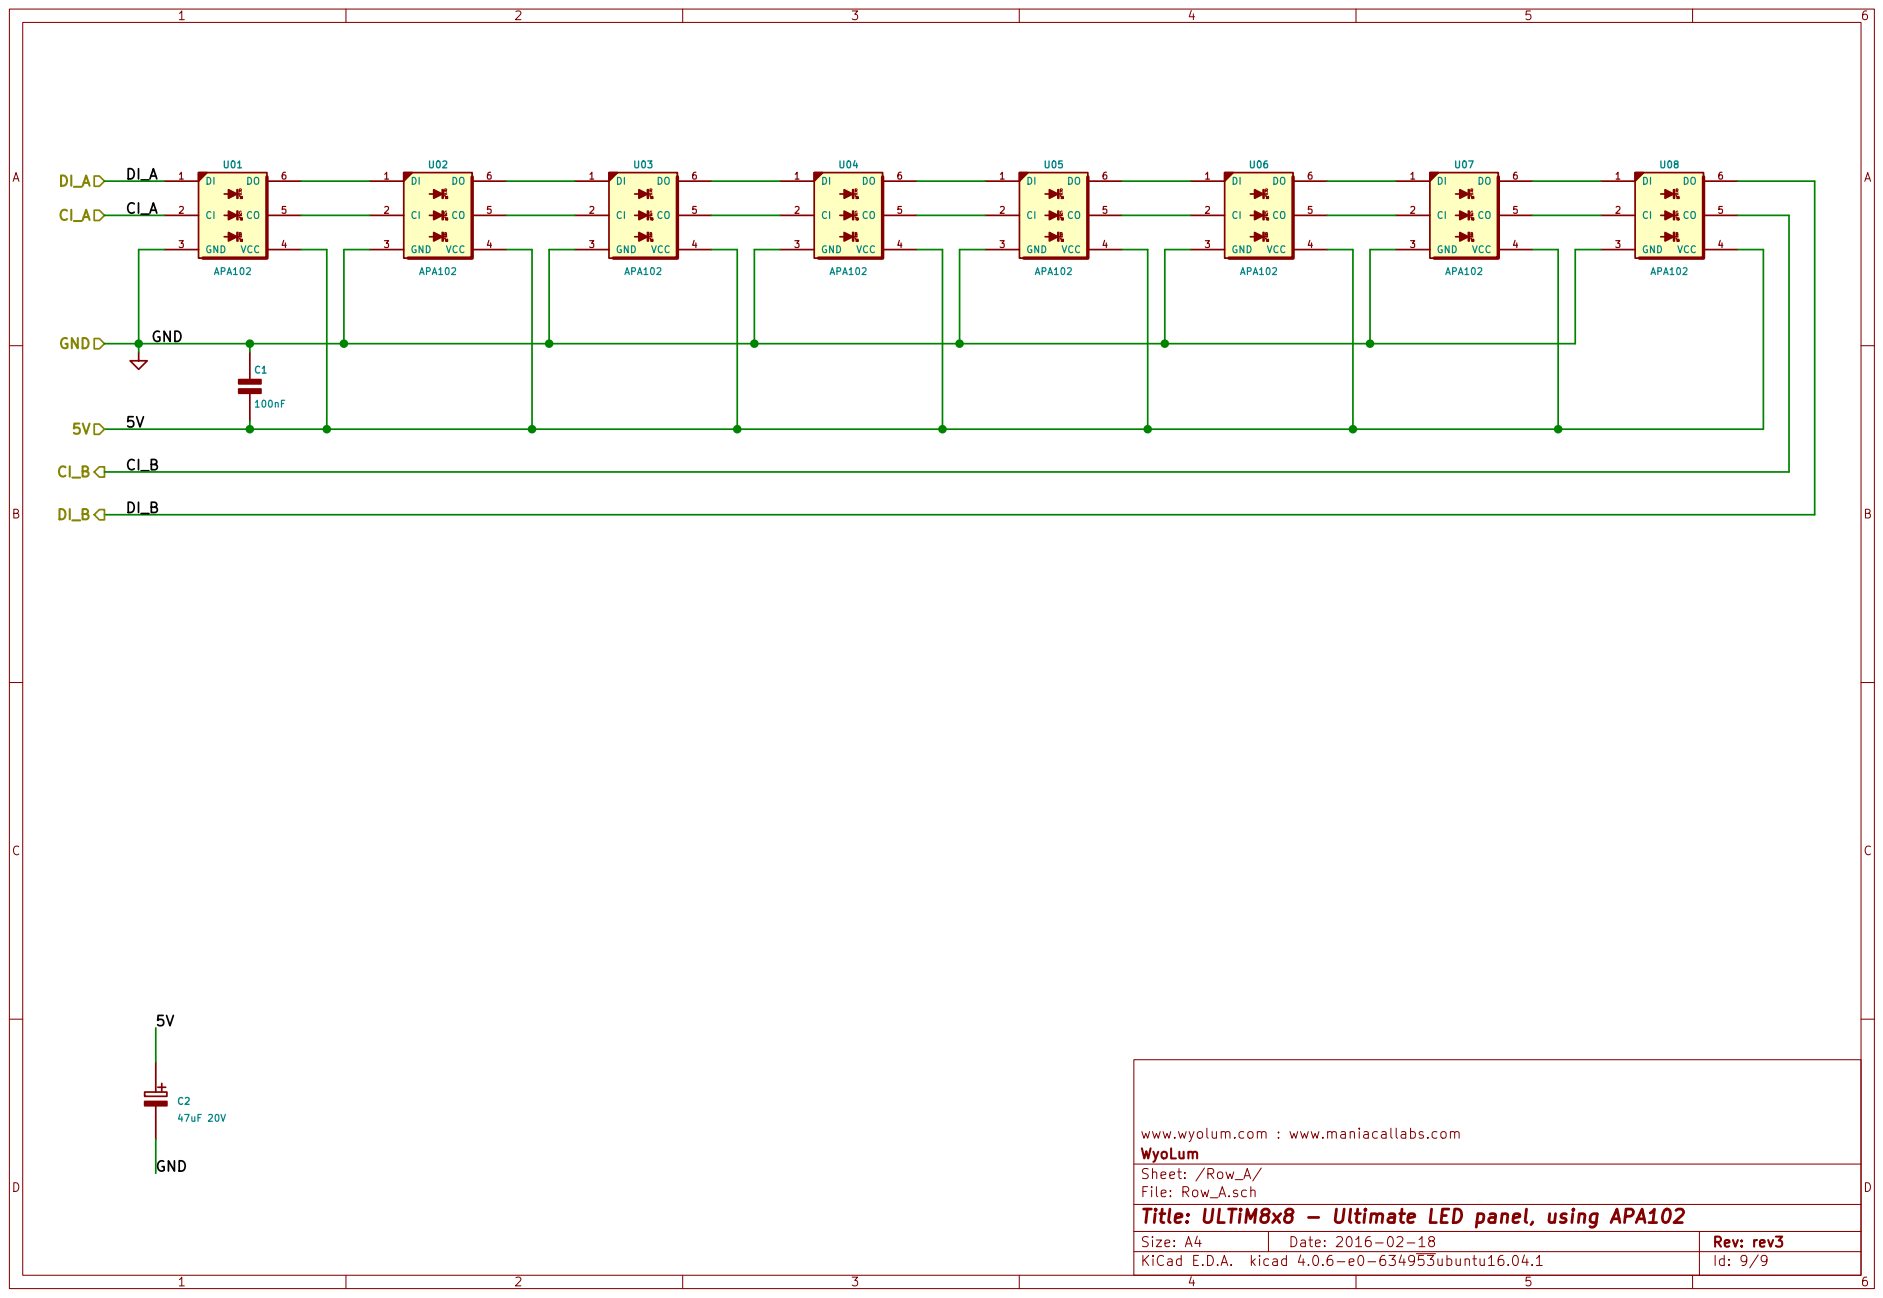
[picture p109: page 9]

www.wyolum.com : www.maniacallabs.com
WyoLum
Sheet: /Row_A/
File: Row_A.sch
Id: 9/9 Title: ULTiM8x8 - Ultimate LED panel, using APA102
