wyolum/ultim8x8/kicad/ultim_bus_v5/ultim_bus_pdf/ultim_bus-F.SilkS.pdf

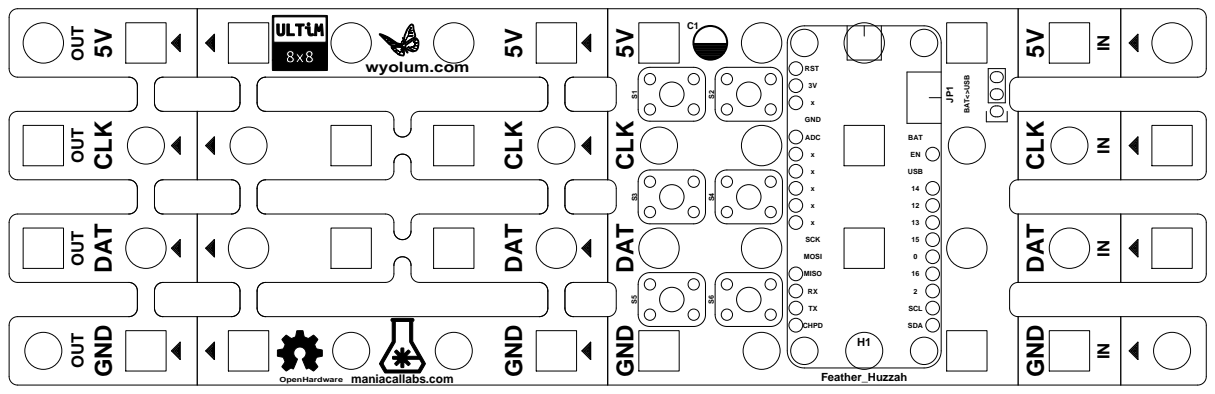
[picture p110: page 1]

BAT MOSI SCK GND
