wyolum/ultim8x8/kicad/ultim_bus_v5/ultim_bus_pdf/ultim_bus.pdf

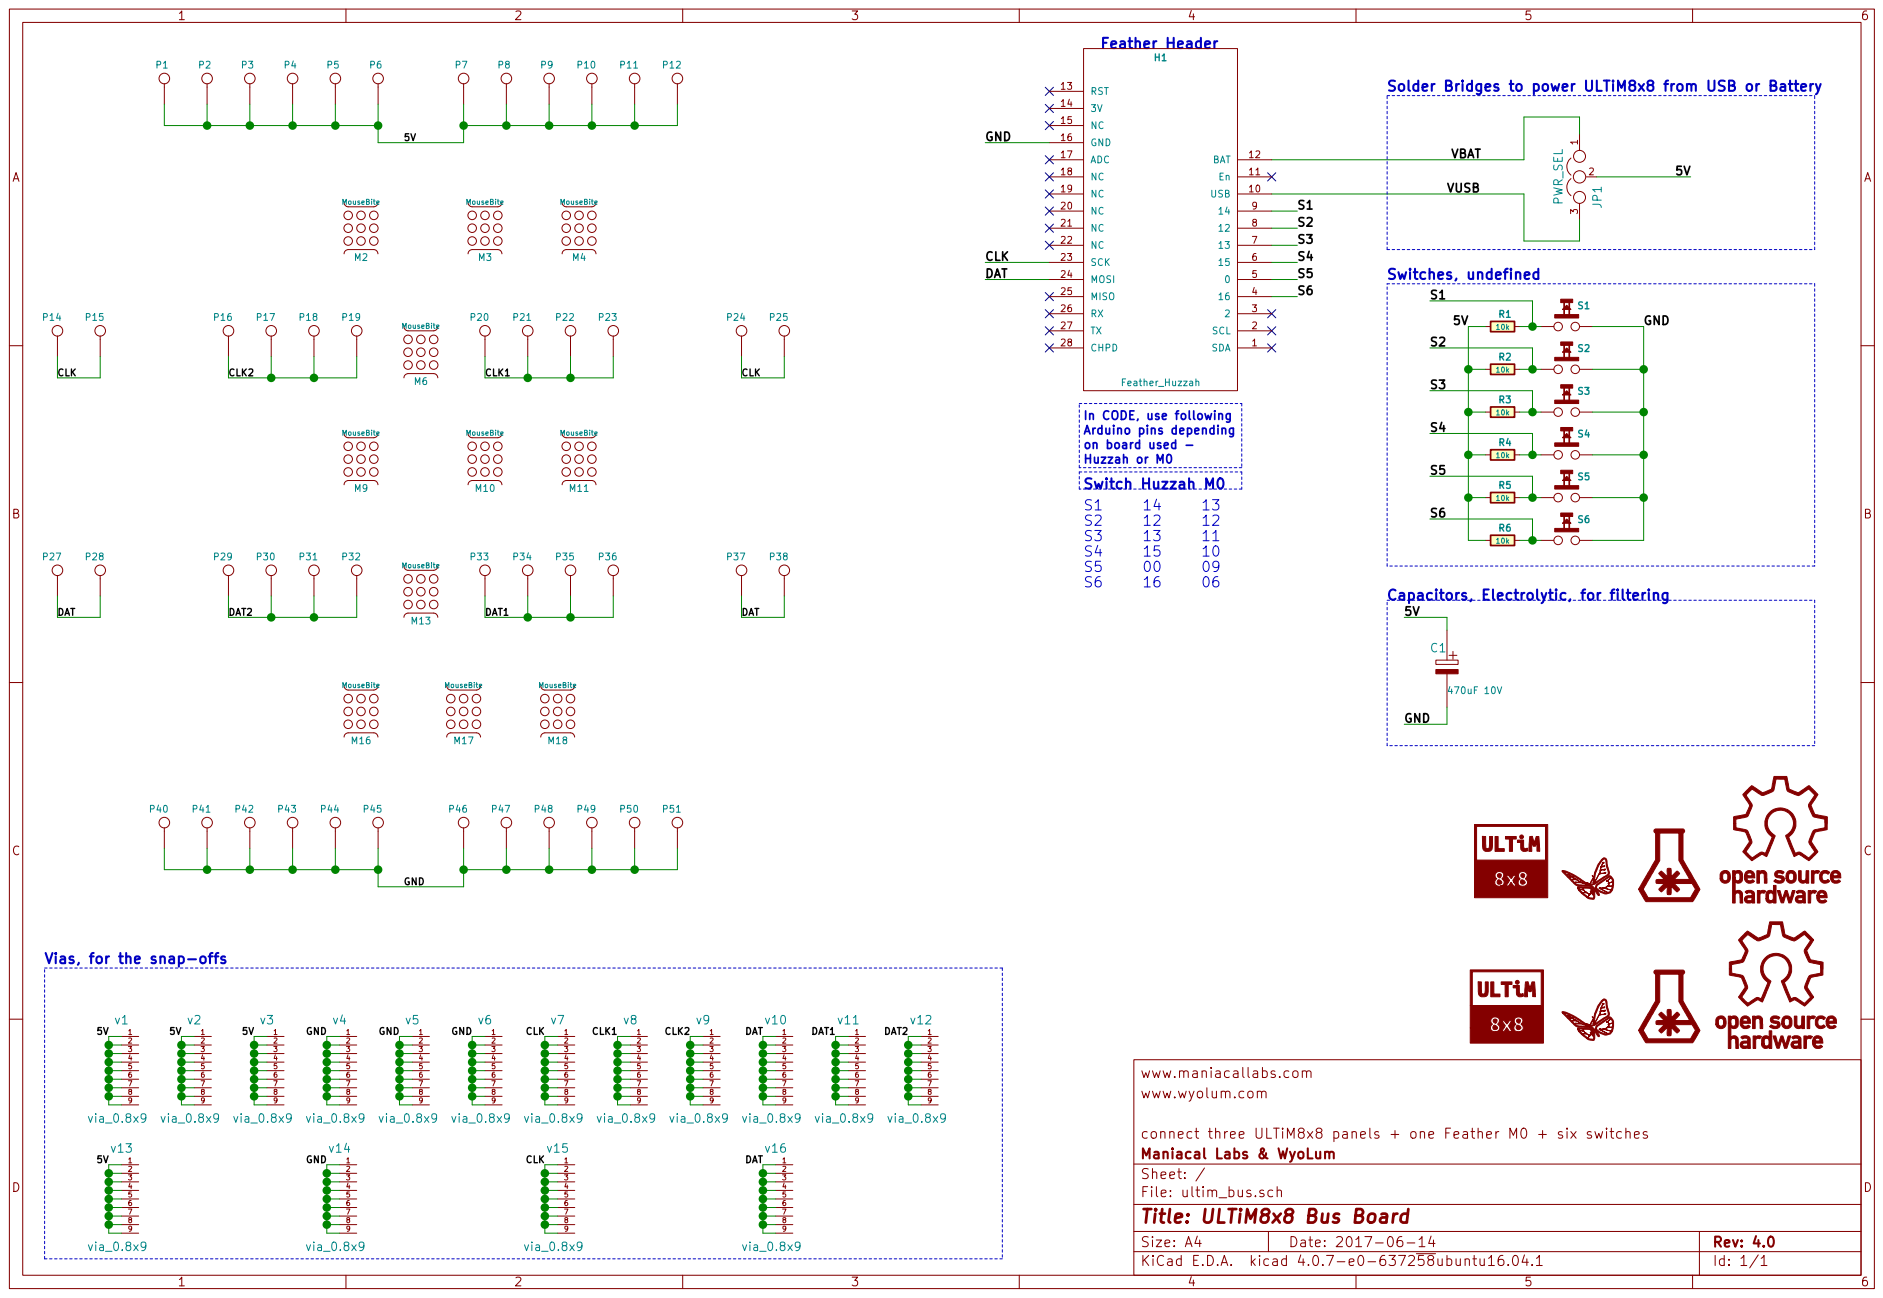
[picture p111: page 1]

In CODE, use following
Arduino pins depending
on board used - Huzzah or M0

470uF 10V 5VGND Capacitors, Electrolytic, for filtering

connect three ULTiM8x8 panels + one Feather M0 + six switches
File: ultim_bus.sch Sheet: / Maniacal Labs & WyoLum

Id: 1/1 Title: ULTiM8x8 Bus Board
