wyolum/ultim8x8/kicad/feather_v3/feather_v3_pdf/feather_v3-F.SilkS.pdf

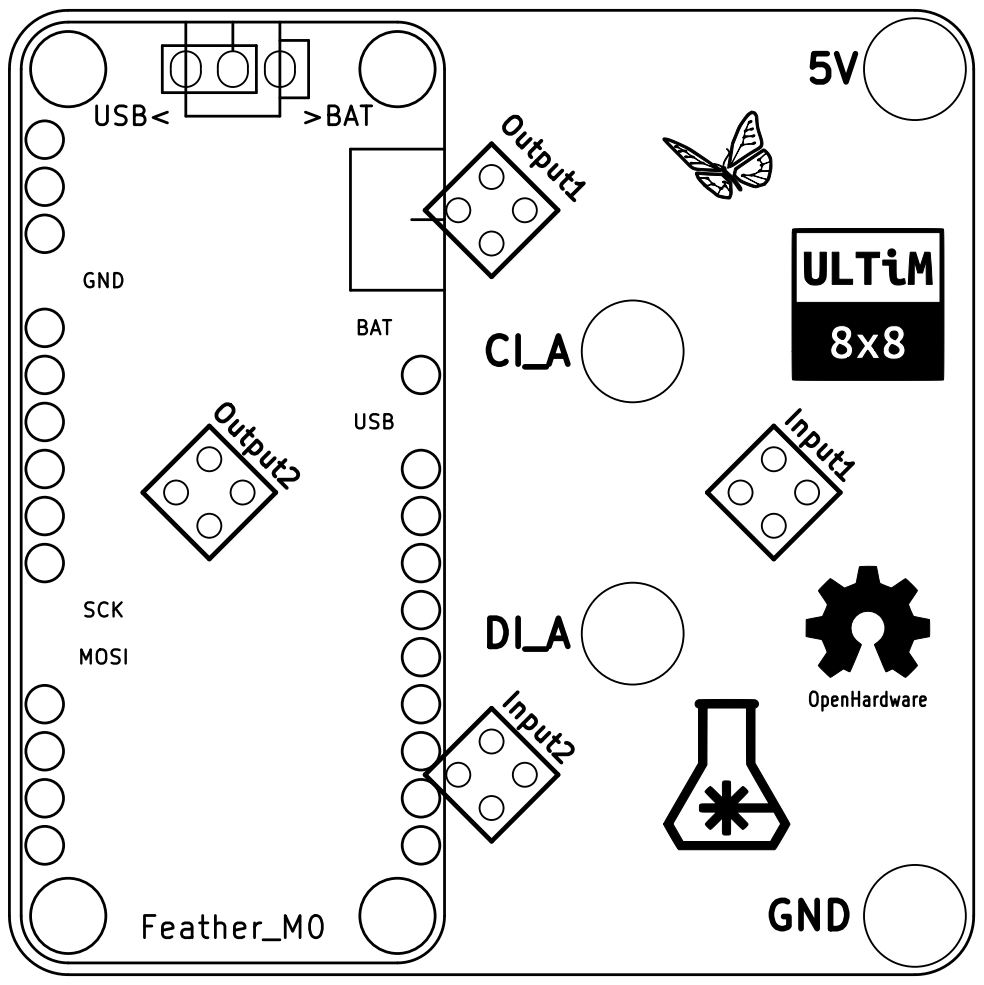
[picture p112: page 1]

BAT MOSI SCK GND
