wyolum/ultim8x8/kicad/feather_v3/feather_v3_pdf/feather_v3.pdf

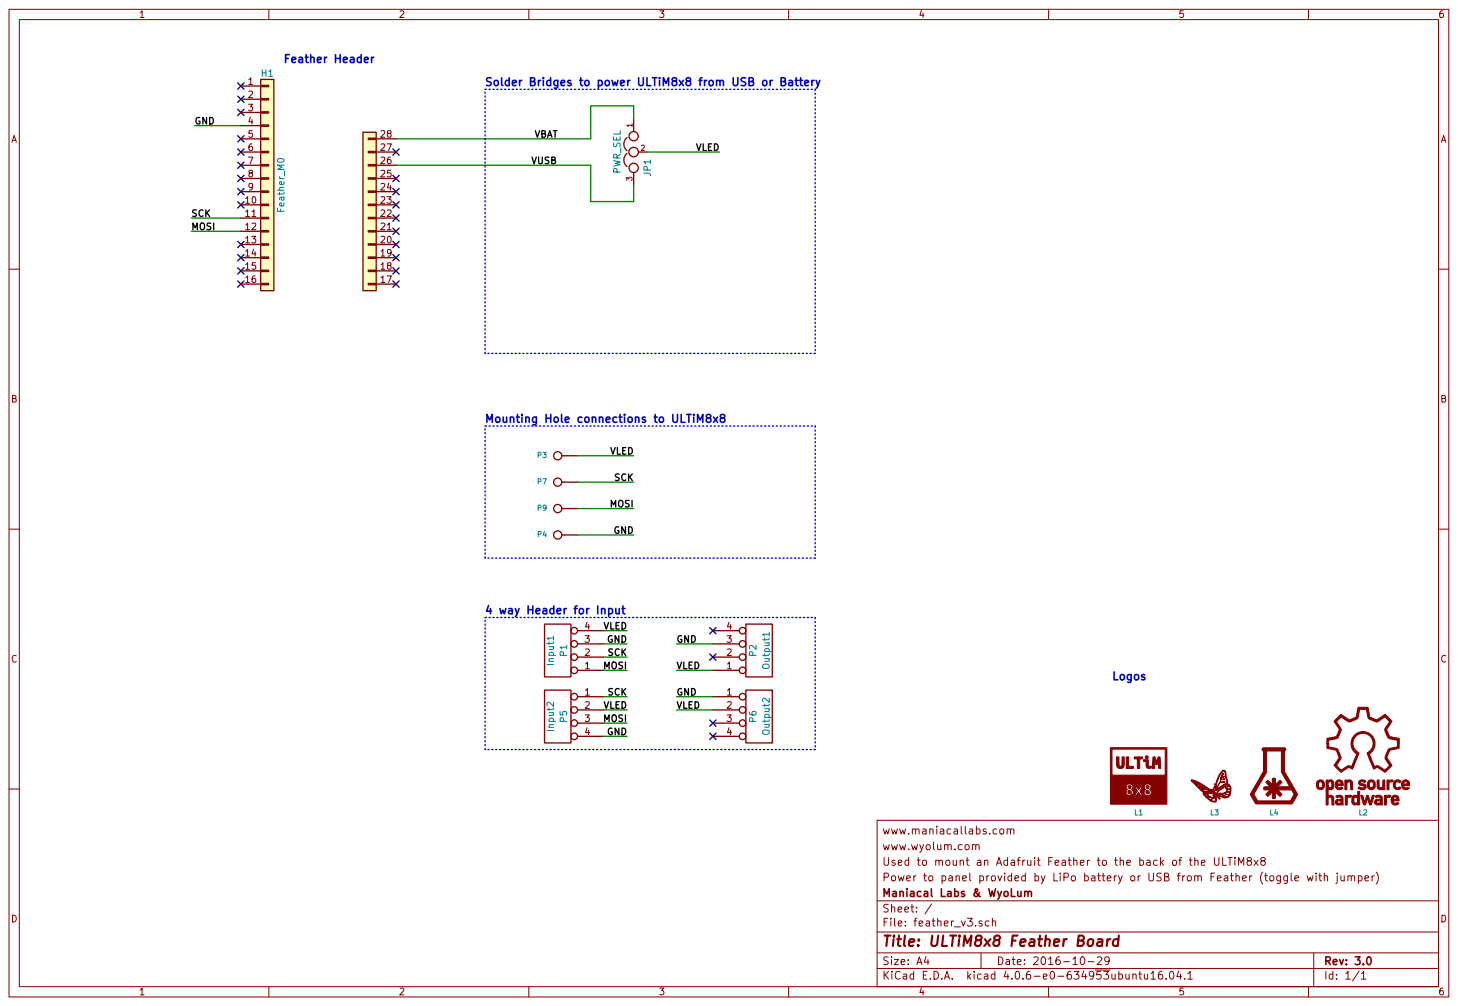
[picture p113: page 1]

SCK MOSI Mounting Hole connections to ULTiM8x8

4 way Header for Input

www.maniacallabs.com
Power to panel provided by LiPo battery or USB from Feather (toggle with jumper) Used to mount an Adafruit Feather to the back of the ULTiM8x8 www.wyolum.com

File: feather_v3.sch Sheet: / Maniacal Labs & WyoLum

Id: 1/1 Title: ULTiM8x8 Feather Board
