wyolum/ultim8x8/kicad/ultim_8x8_v2/ultim8x8_pdf/v1/ultim8x8-B.SilkS.pdf

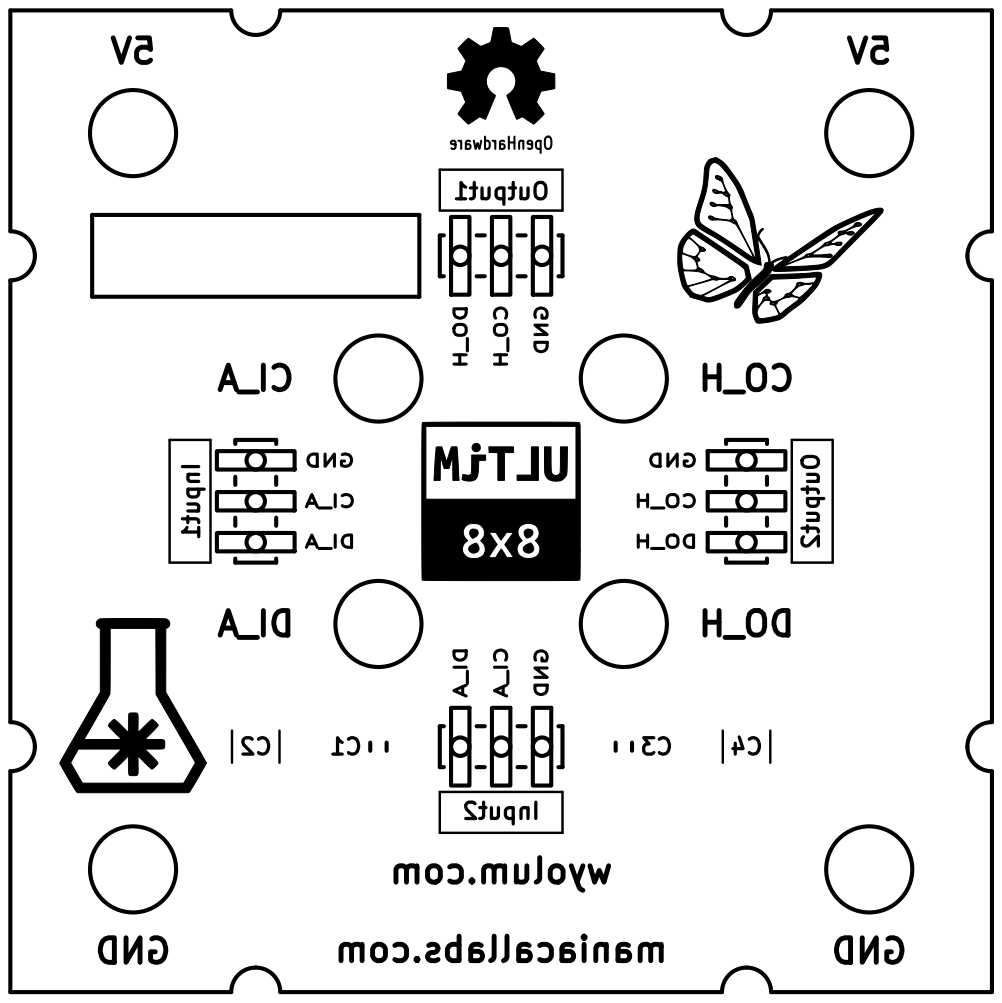
[picture p114: page 1]

File: ultim8x8.kicad_pcb Sheet: wyolum.com
