wyolum/ultim8x8/kicad/ultim_bus_conn/ultim_bus_conn_pdf/ultim_bus_conn-B.SilkS.pdf

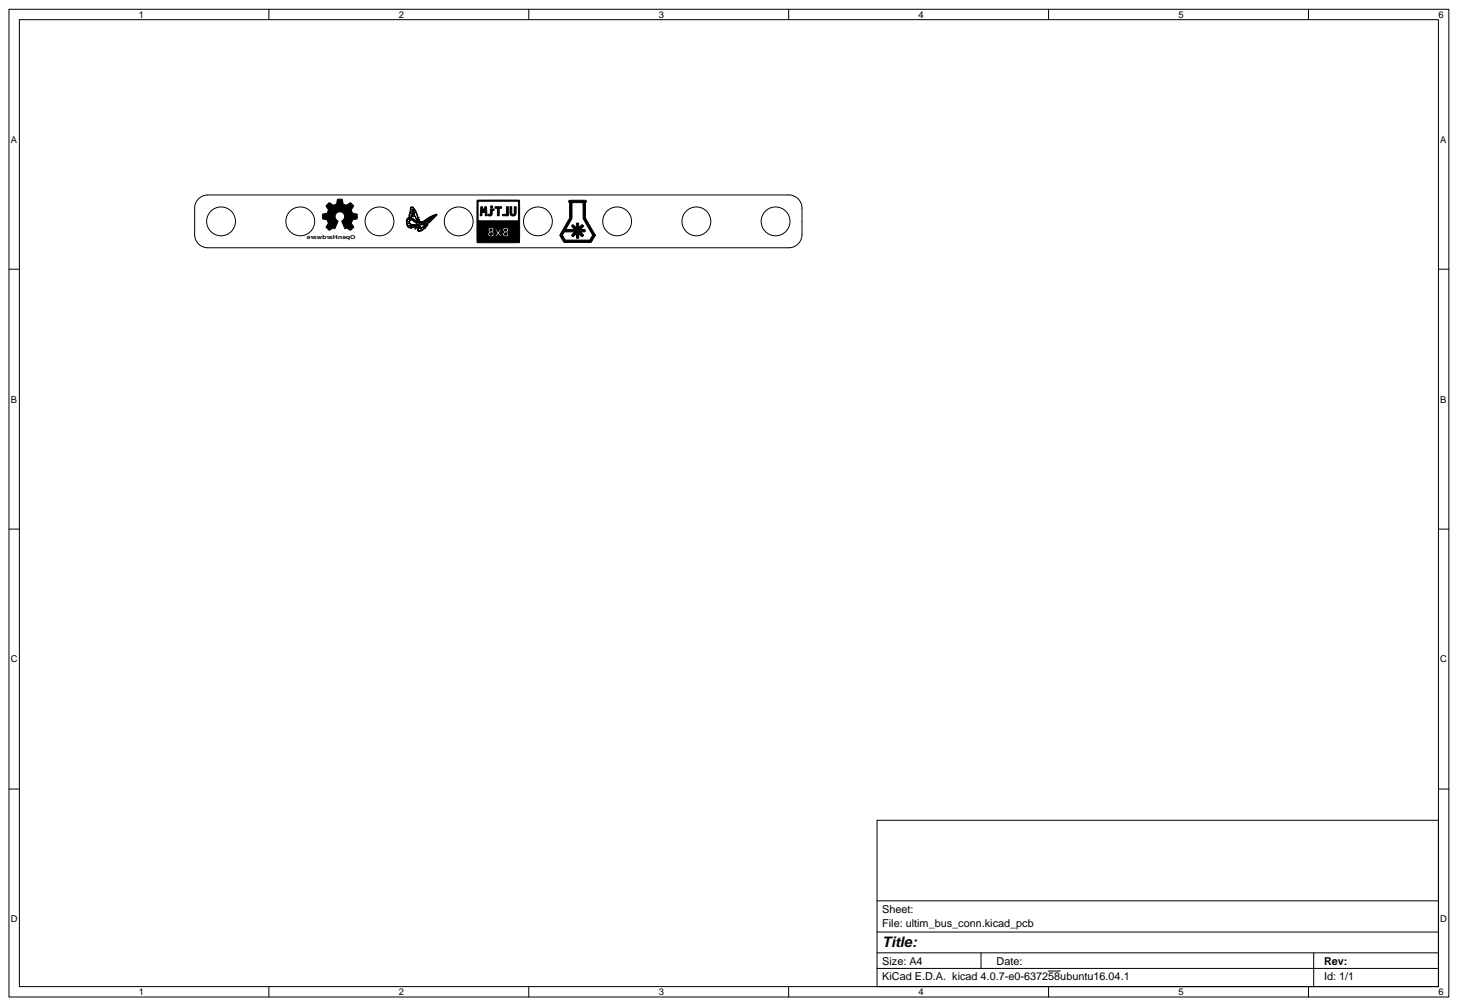
[picture p125: page 1]
