wyolum/ultim8x8/kicad/ultim_bus_conn/ultim_bus_conn_pdf/ultim_bus_conn-Dwgs.User.pdf

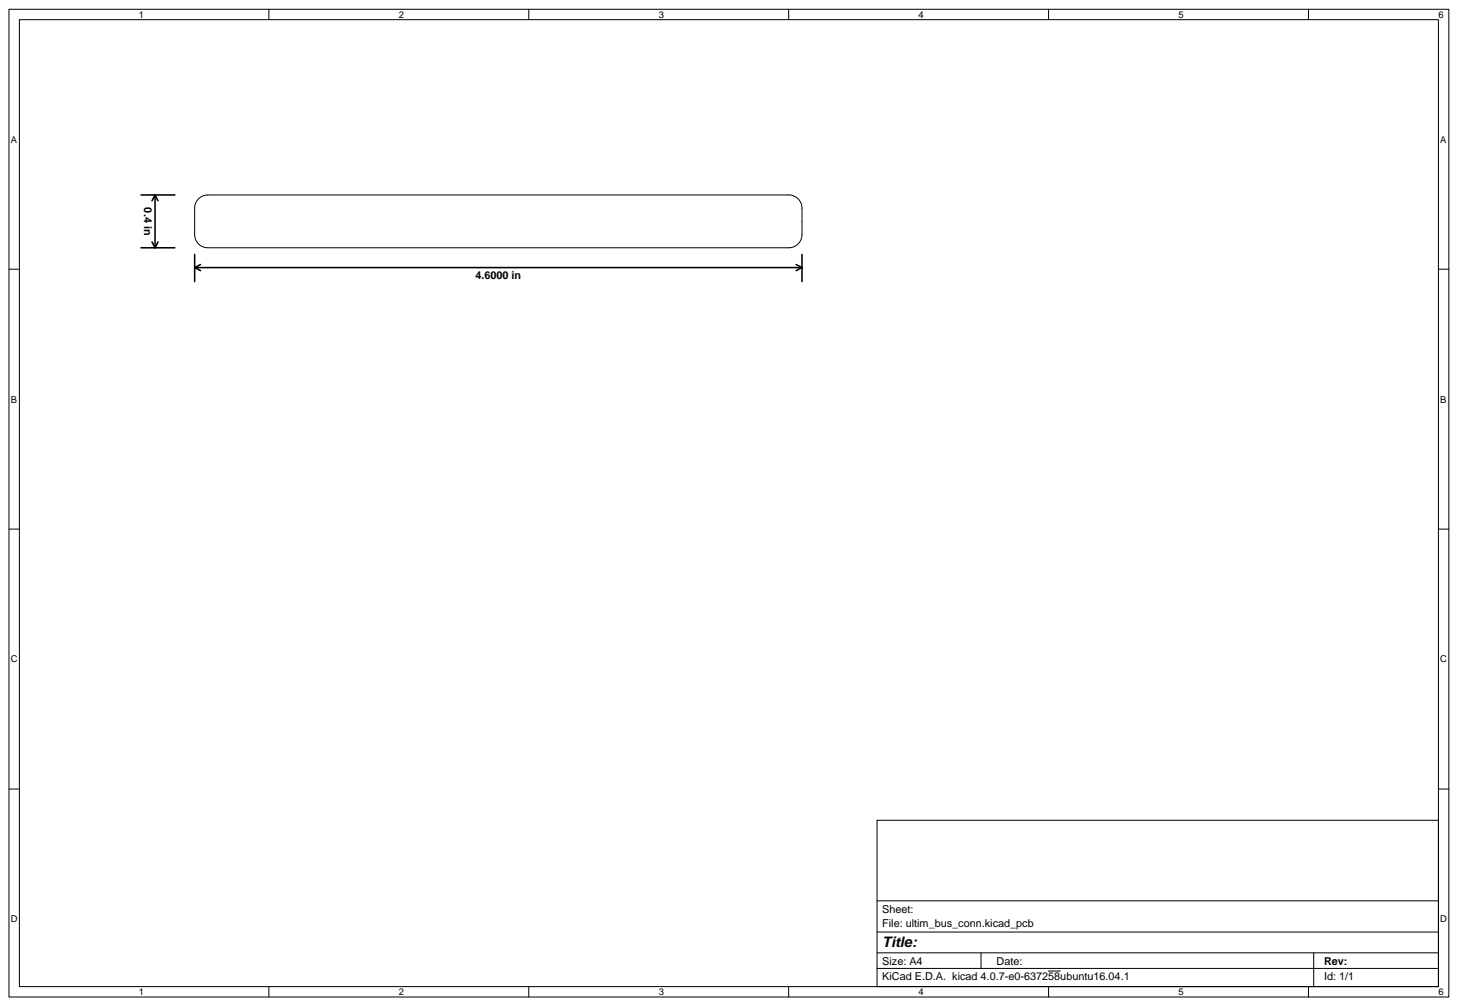
[picture p126: page 1]
