wyolum/ultim8x8/kicad/ultim_bus_conn/ultim_bus_conn_pdf/ultim_bus_conn-F.SilkS.pdf

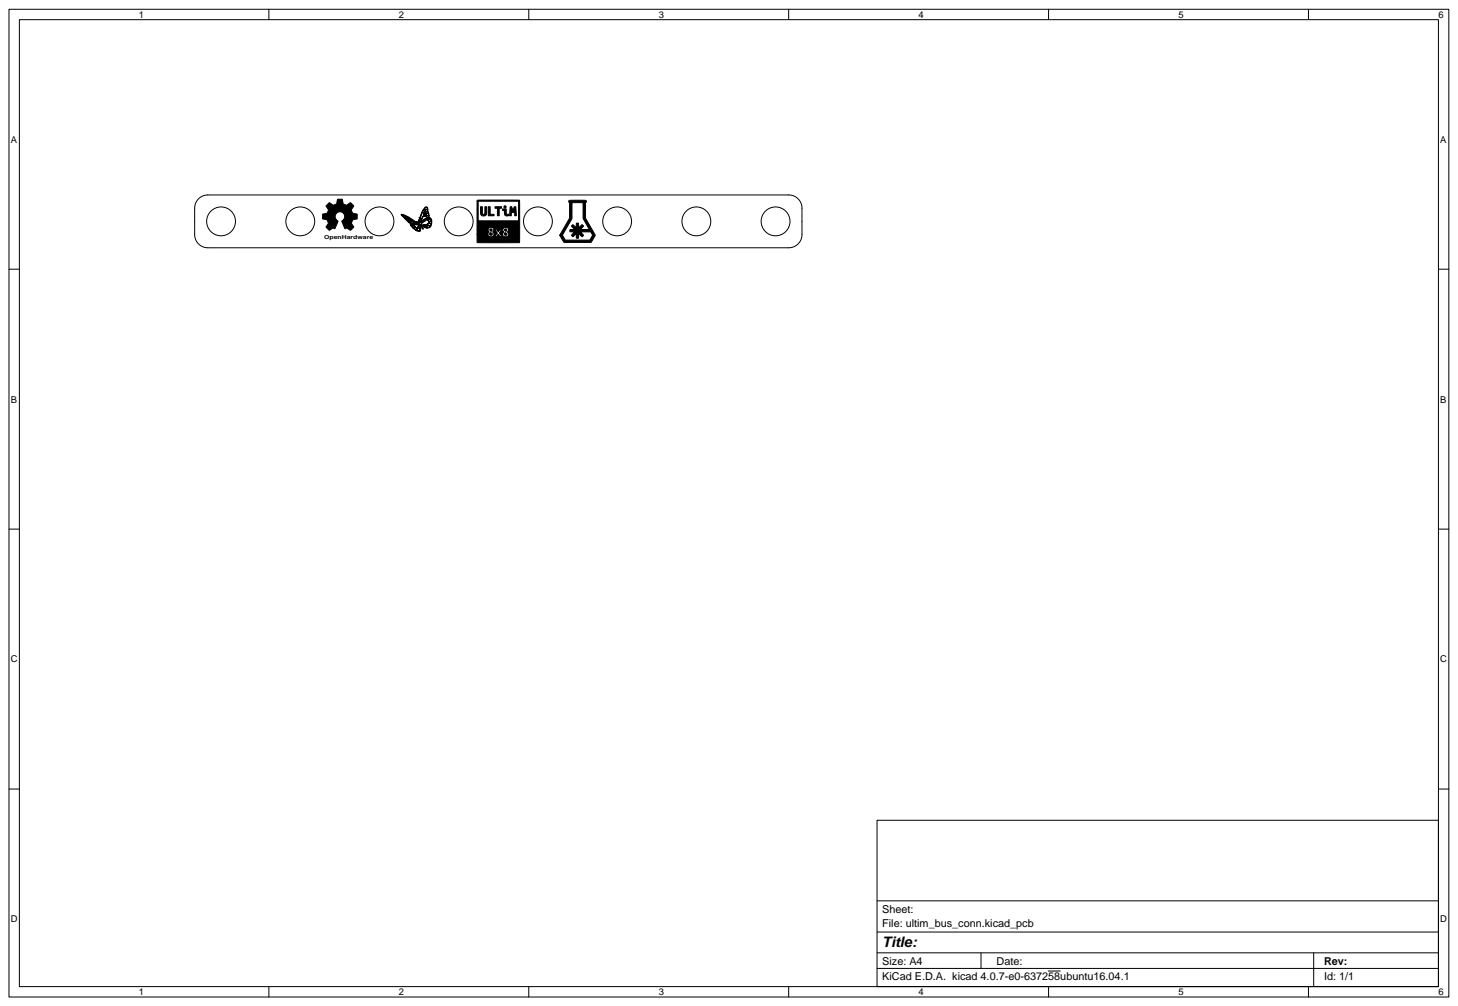
[picture p128: page 1]
