wyolum/ultim8x8/kicad/ultim_bus_v5/ultim_bus_pdf/ultim_bus-B.Cu.pdf

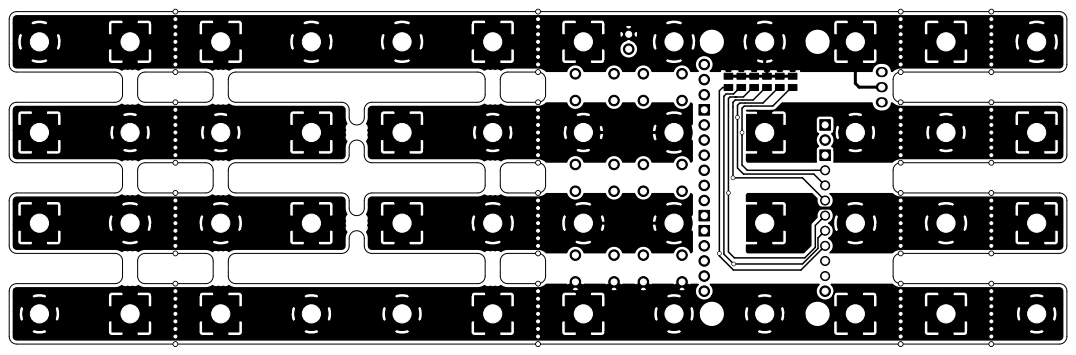
[picture p129: page 1]
