wyolum/ultim8x8/kicad/ultim_bus_v5/ultim_bus_pdf/ultim_bus-B.SilkS.pdf

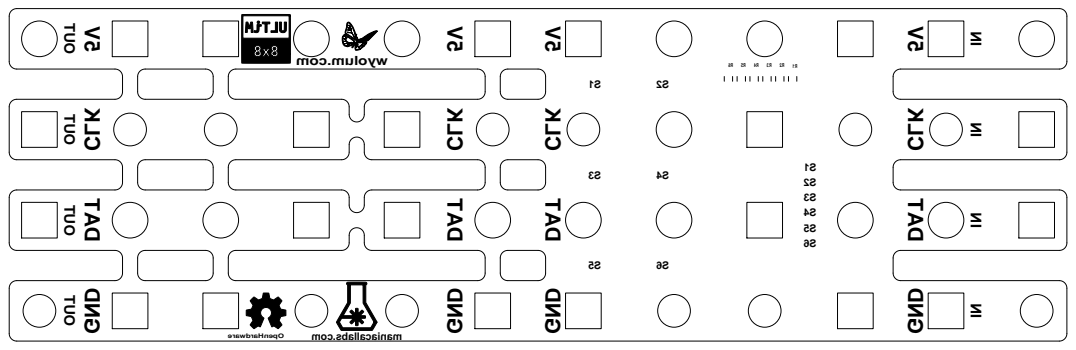
[picture p130: page 1]
