wyolum/ultim8x8/kicad/ultim_bus_v5/ultim_bus_pdf/ultim_bus-Dwgs.User.pdf

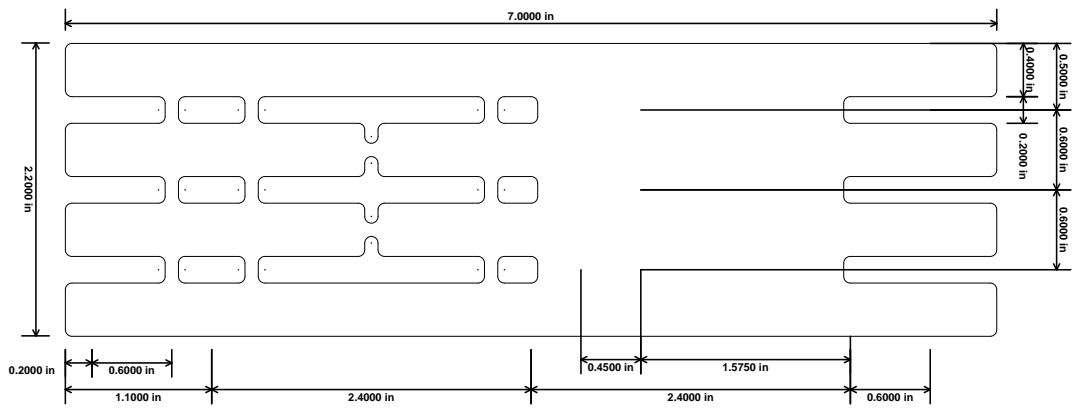
[picture p131: page 1]
