wyolum/ultim8x8/kicad/ultim_bus_v5/ultim_bus_pdf/ultim_bus-F.Cu.pdf

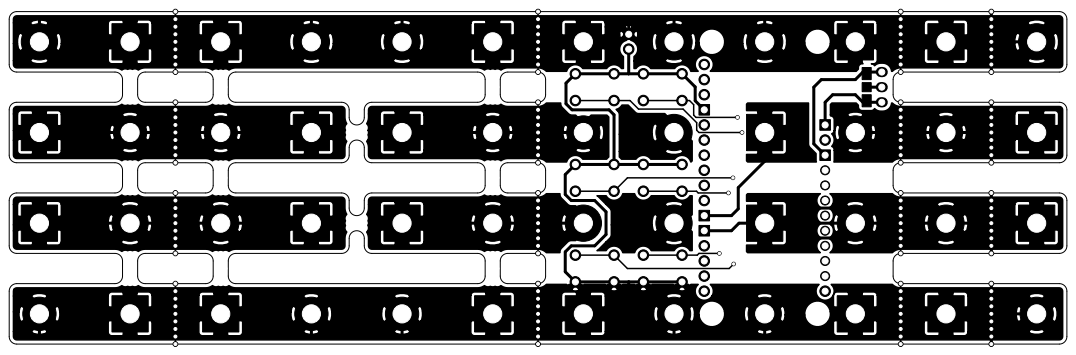
[picture p132: page 1]
