wyolum/ultim8x8/kicad/feather_v3/feather_v3_pdf/feather_v3-B.Cu.pdf

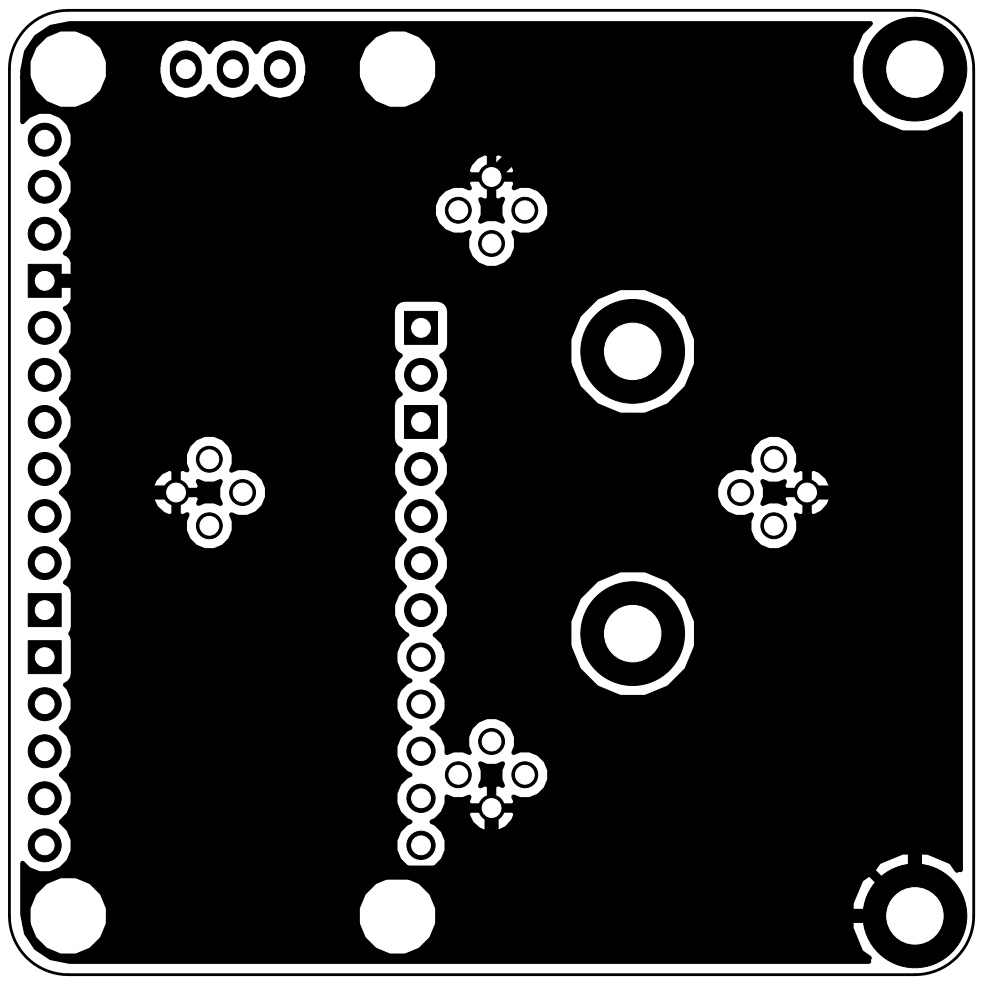
[picture p133: page 1]
