wyolum/ultim8x8/kicad/feather_v3/feather_v3_pdf/feather_v3-Dwgs.User.pdf

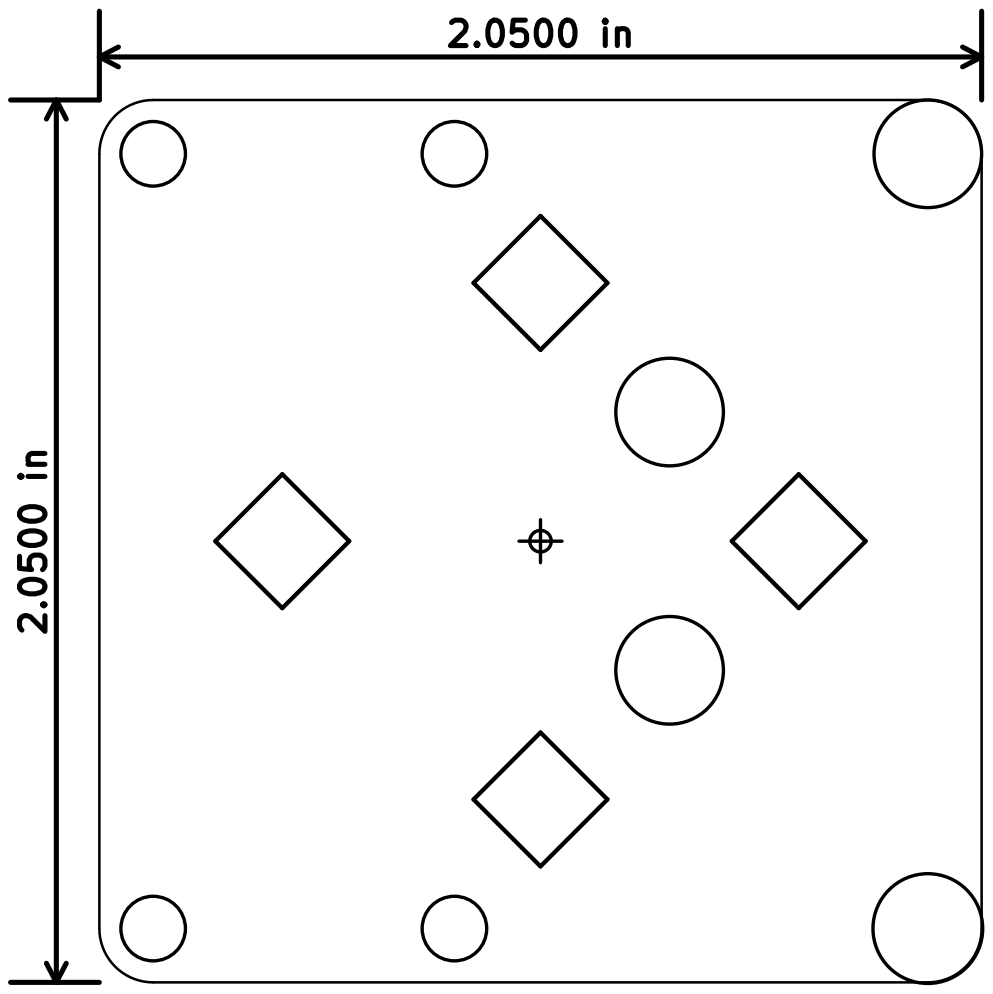
[picture p135: page 1]
