wyolum/ultim8x8/kicad/feather_v3/feather_v3_pdf/feather_v3-F.Cu.pdf

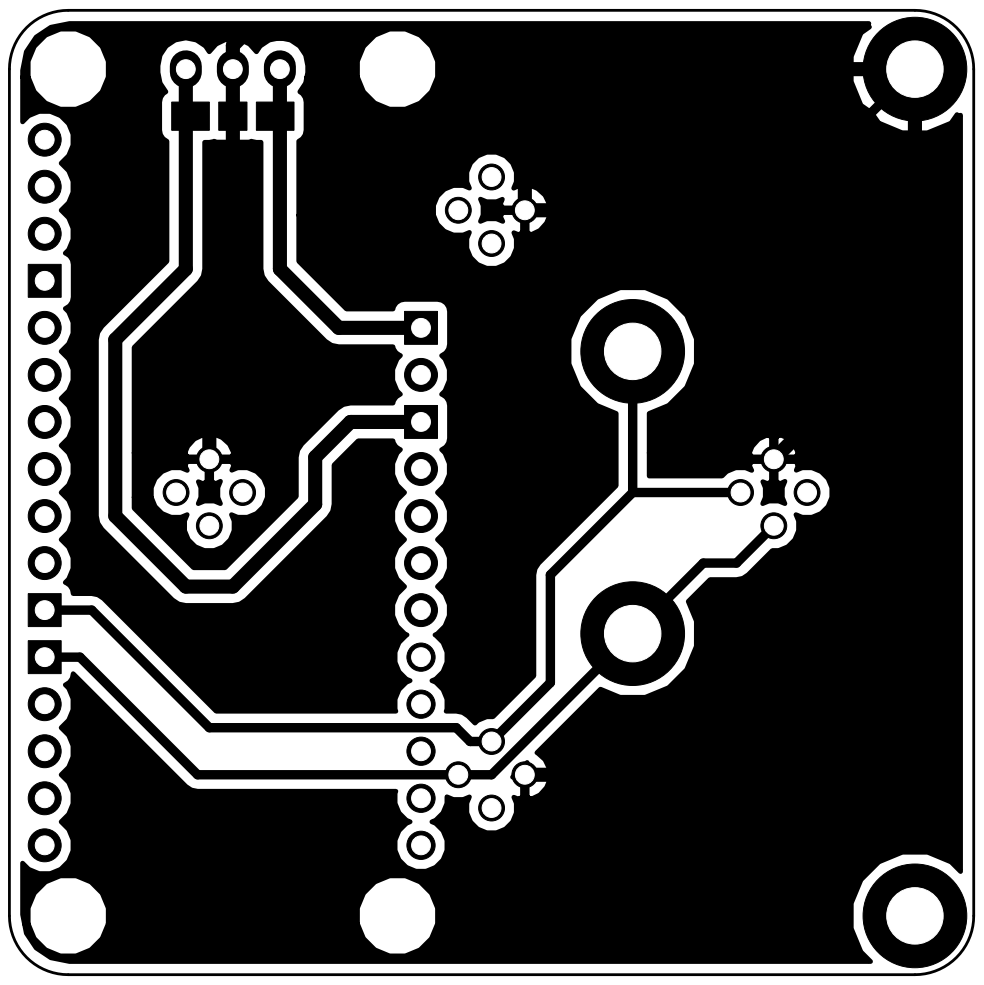
[picture p136: page 1]
