wyolum/ultim8x8/kicad/ultim_8x8_v2/ultim8x8_pdf/v1/ultim_bus-B.Cu.pdf

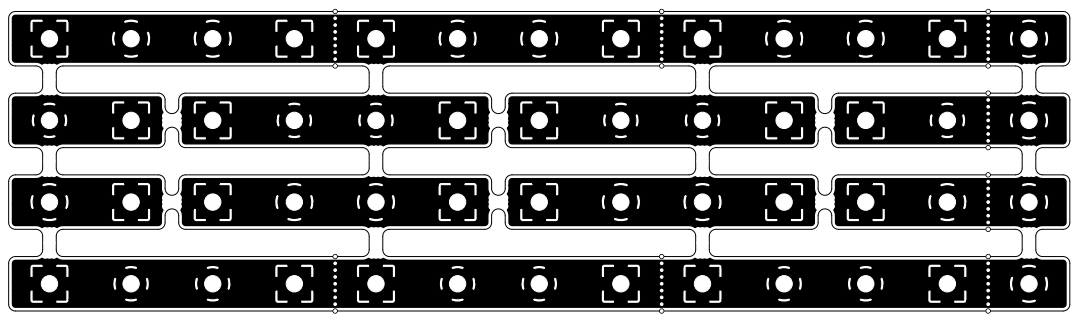
[picture p137: page 1]
