wyolum/ultim8x8/kicad/ultim_8x8_v2/ultim8x8_pdf/v1/ultim8x8-Edge.Cuts.pdf

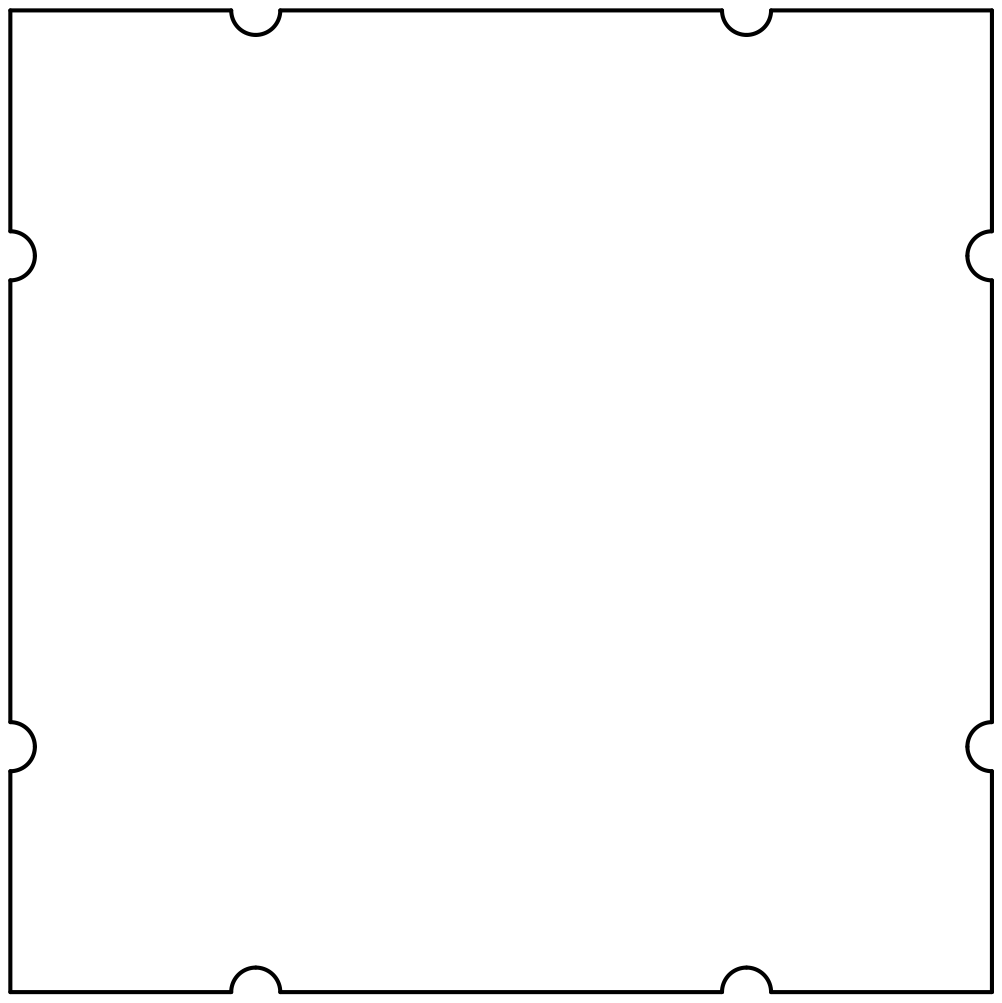
[picture p144: page 1]
