wyolum/ultim8x8/kicad/ultim_bus_v4/ultim_bus_pdf/ultim_bus-B.Cu.pdf

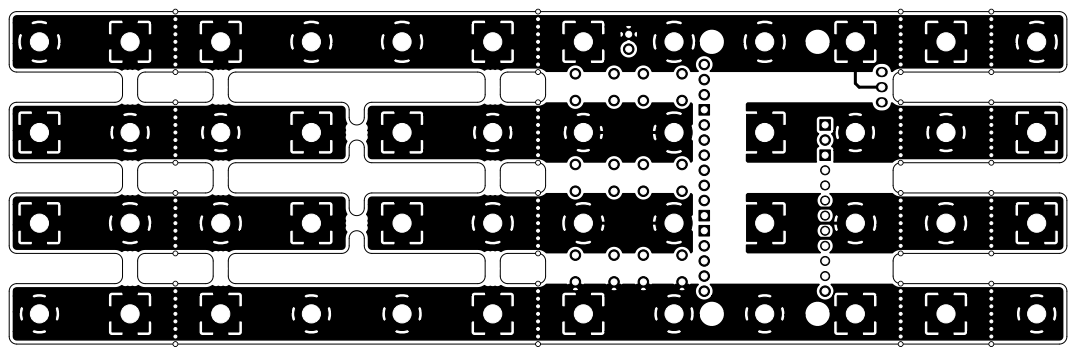
[picture p150: page 1]
