wyolum/ultim8x8/kicad/ultim_bus_v4/ultim_bus_pdf/ultim_bus-B.SilkS.pdf

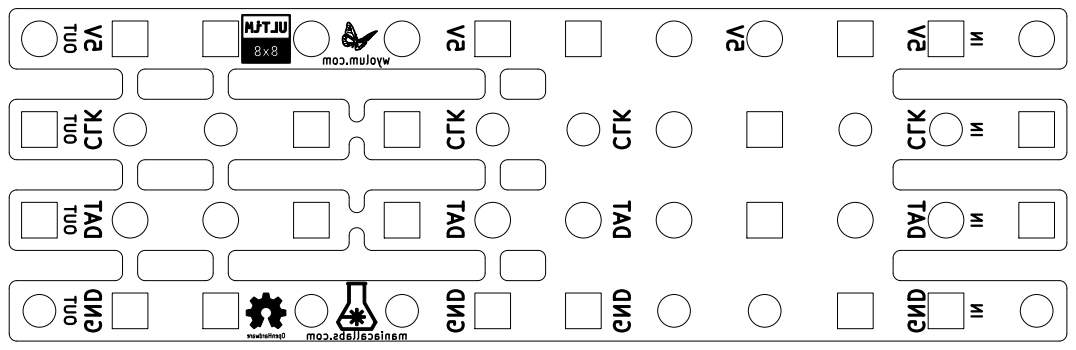
[picture p151: page 1]
