wyolum/ultim8x8/kicad/ultim_bus_v4/ultim_bus_pdf/ultim_bus-Dwgs.User.pdf

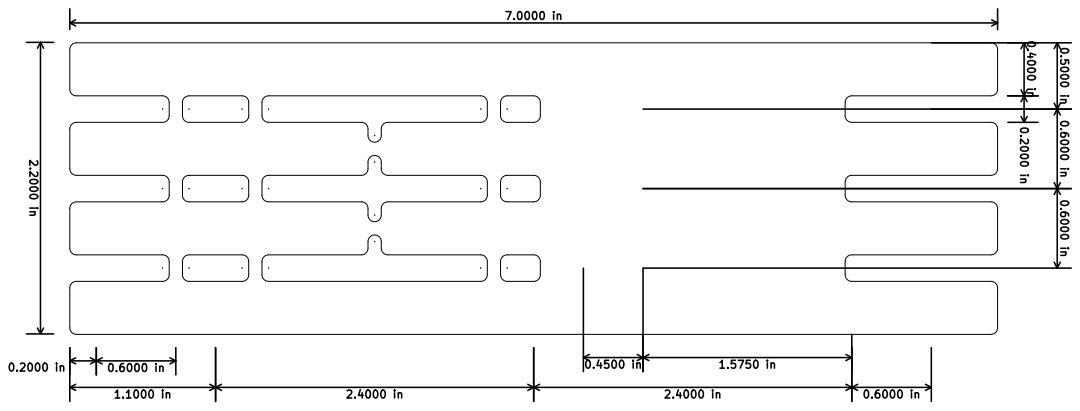
[picture p152: page 1]
