wyolum/ultim8x8/kicad/ultim_bus_v4/ultim_bus_pdf/ultim_bus-F.SilkS.pdf

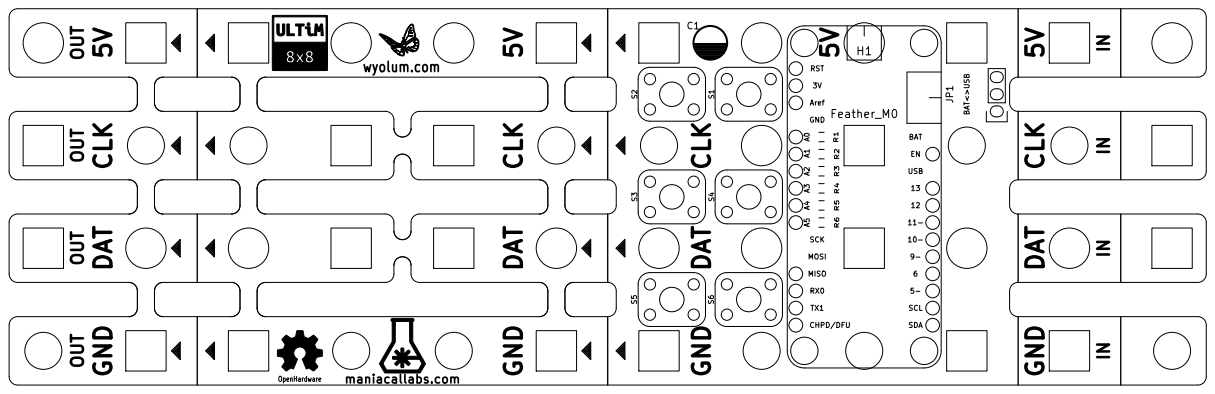
[picture p154: page 1]
