wyolum/ultim8x8/kicad/feather_v2/feather_v2_pdf/feather_v2-B.Cu.pdf

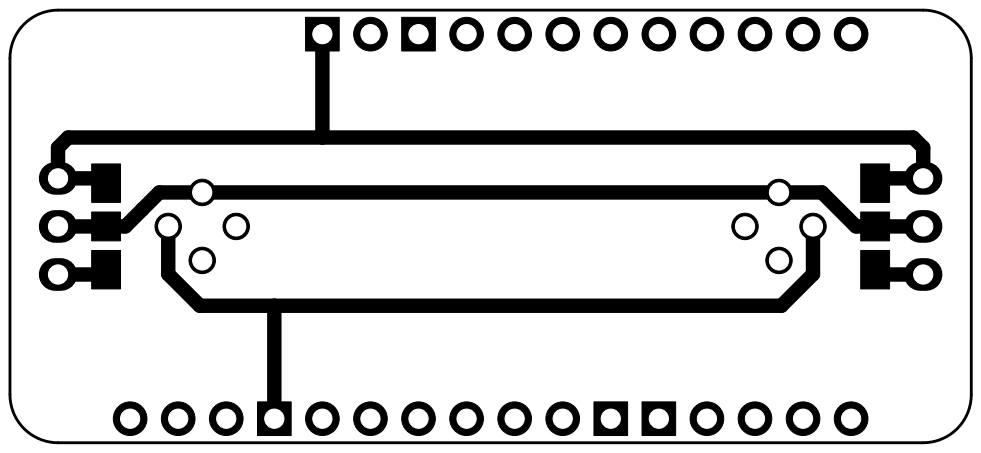
[picture p155: page 1]
