wyolum/ultim8x8/kicad/feather_v2/feather_v2_pdf/feather_v2-B.SilkS.pdf

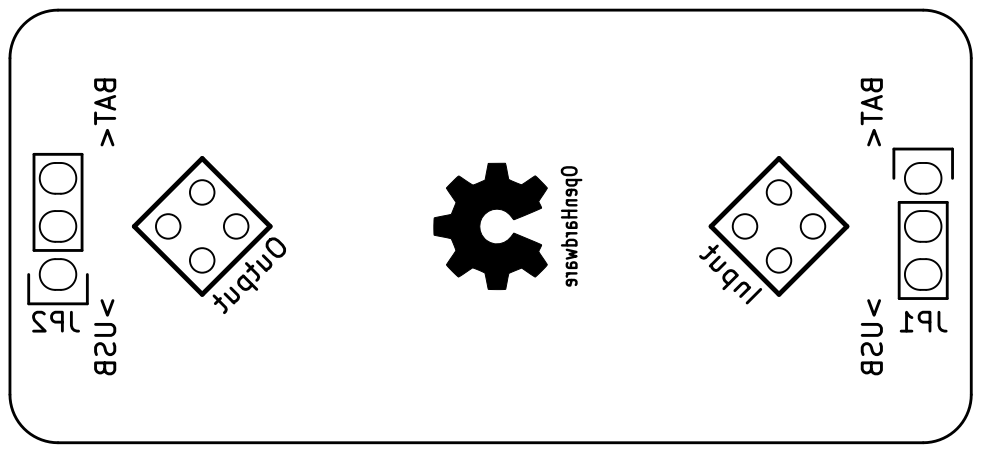
[picture p156: page 1]
