wyolum/ultim8x8/kicad/feather_v2/feather_v2_pdf/feather_v2-Dwgs.User.pdf

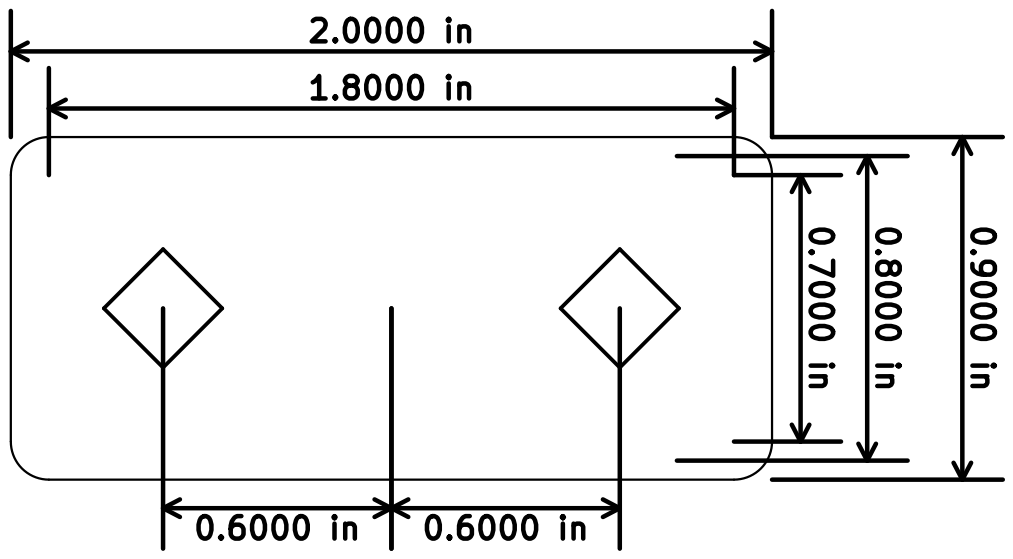
[picture p157: page 1]
