wyolum/ultim8x8/kicad/feather_v2/feather_v2_pdf/feather_v2-F.Cu.pdf

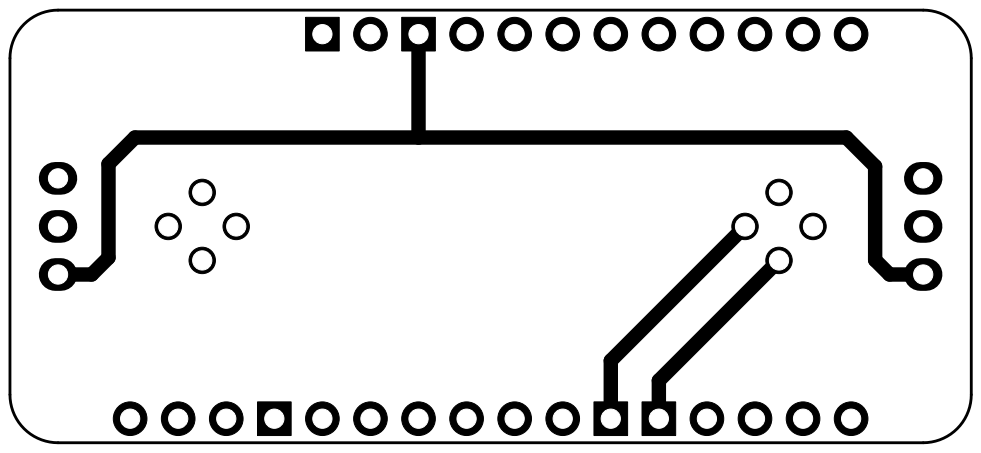
[picture p158: page 1]
