wyolum/ultim8x8/kicad/ultim_bus_v1/ultim_bus_pdf/ultim_bus-B.Cu.pdf

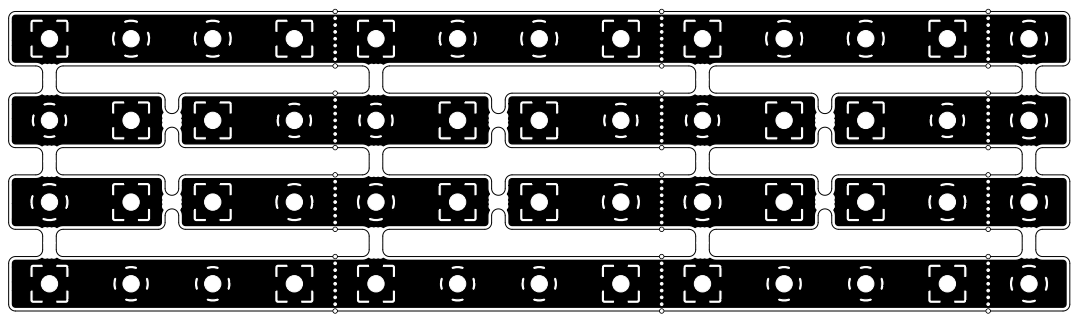
[picture p160: page 1]
