wyolum/ultim8x8/kicad/ultim_bus_v1/ultim_bus_pdf/ultim_bus-B.SilkS.pdf

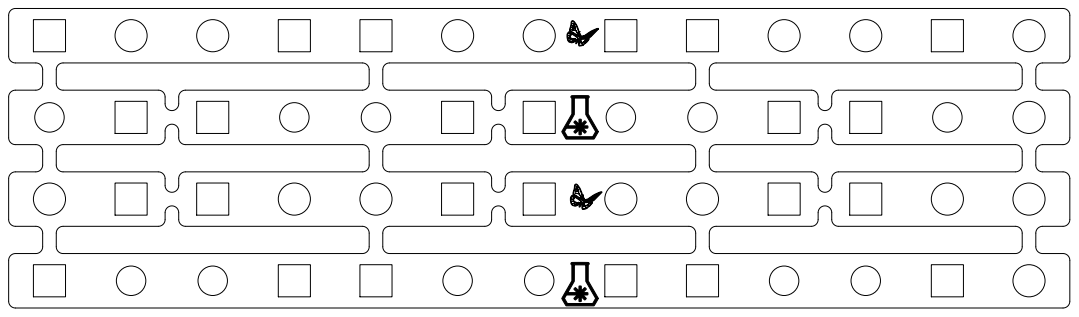
[picture p161: page 1]
