wyolum/ultim8x8/kicad/ultim_bus_v1/ultim_bus_pdf/ultim_bus-F.Cu.pdf

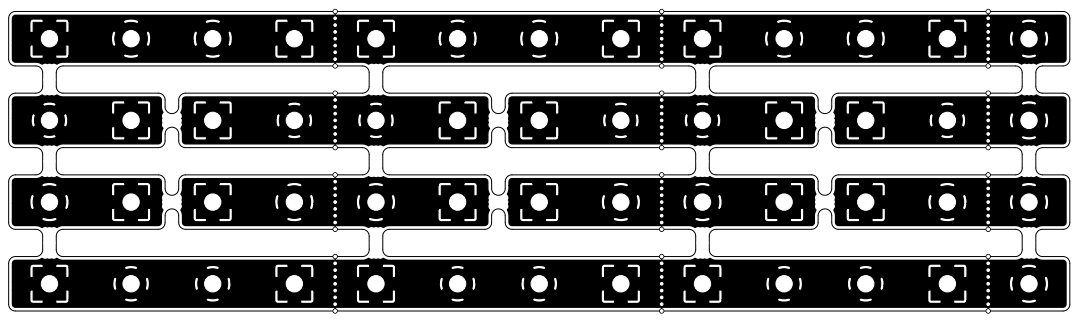
[picture p162: page 1]
