wyolum/ultim8x8/kicad/ultim_bus_v1/ultim_bus_pdf/ultim_bus-F.SilkS.pdf

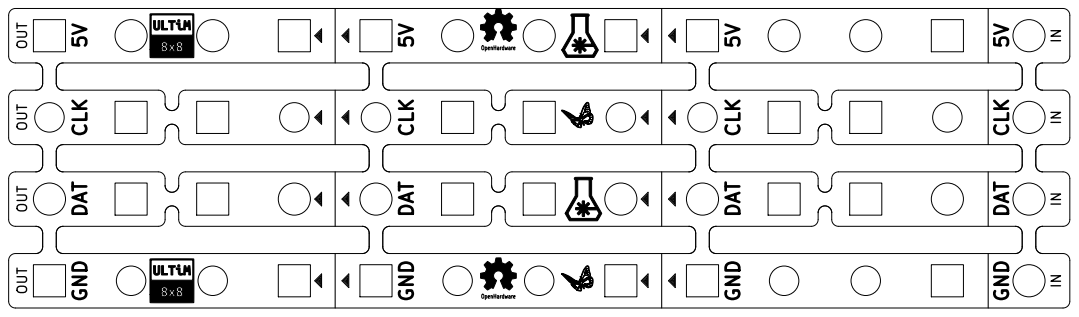
[picture p163: page 1]
