wyolum/ultim8x8/kicad/ultim_8x8_v1/ultim8x8_pdf/ultim8x8-Dwgs.User.pdf

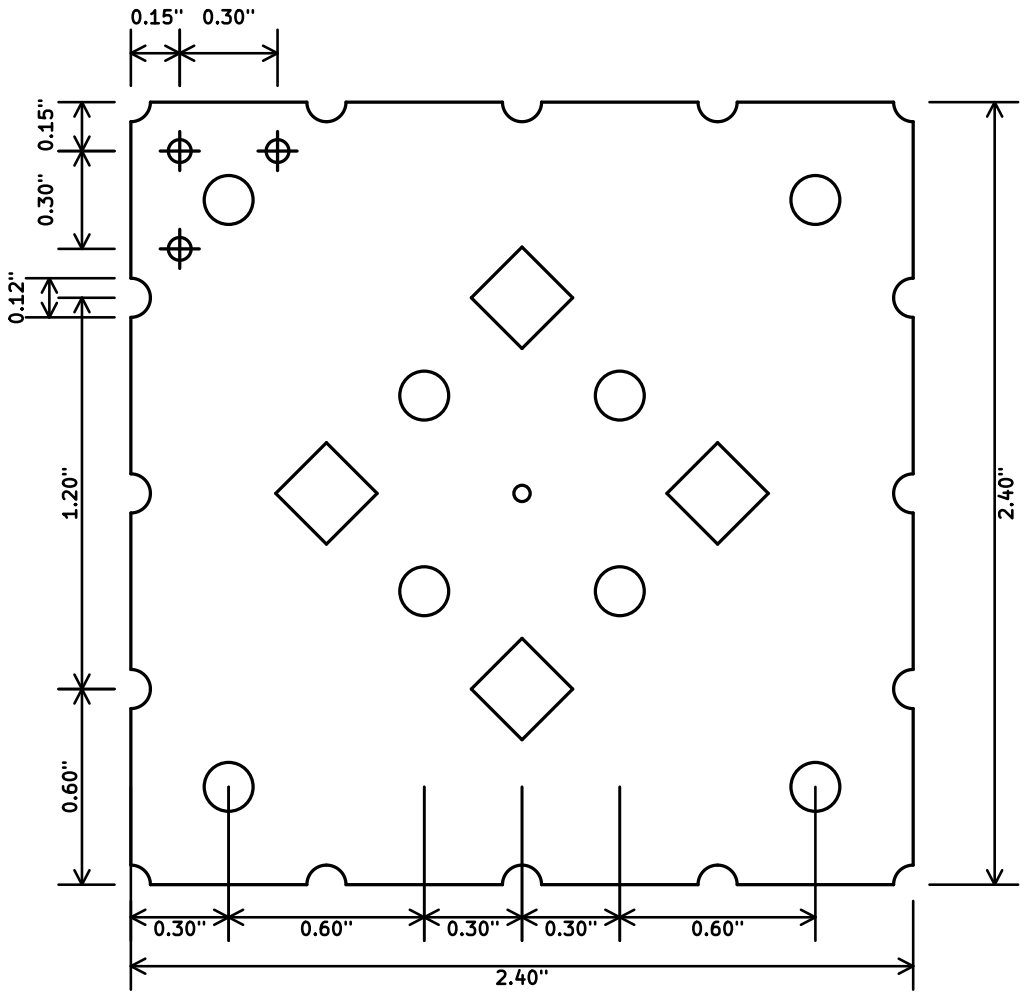
[picture p166: page 1]
