wyolum/ultim8x8/kicad/ultim_8x8_v0/ultim8x8_pdf/ultim8x8-B.SilkS.pdf

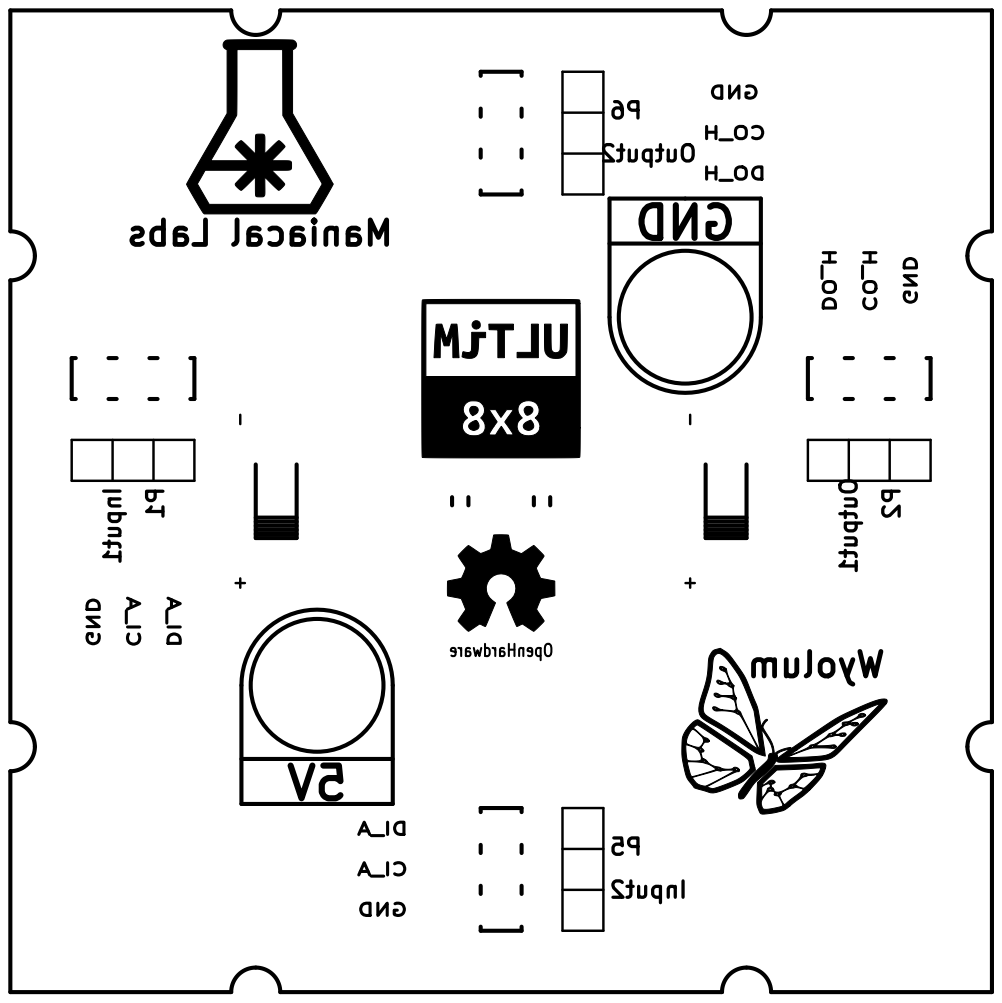
[picture p169: page 1]
