wyolum/ultim8x8/kicad/ultim_8x8_v0/ultim8x8_pdf/ultim8x8-Back.pdf

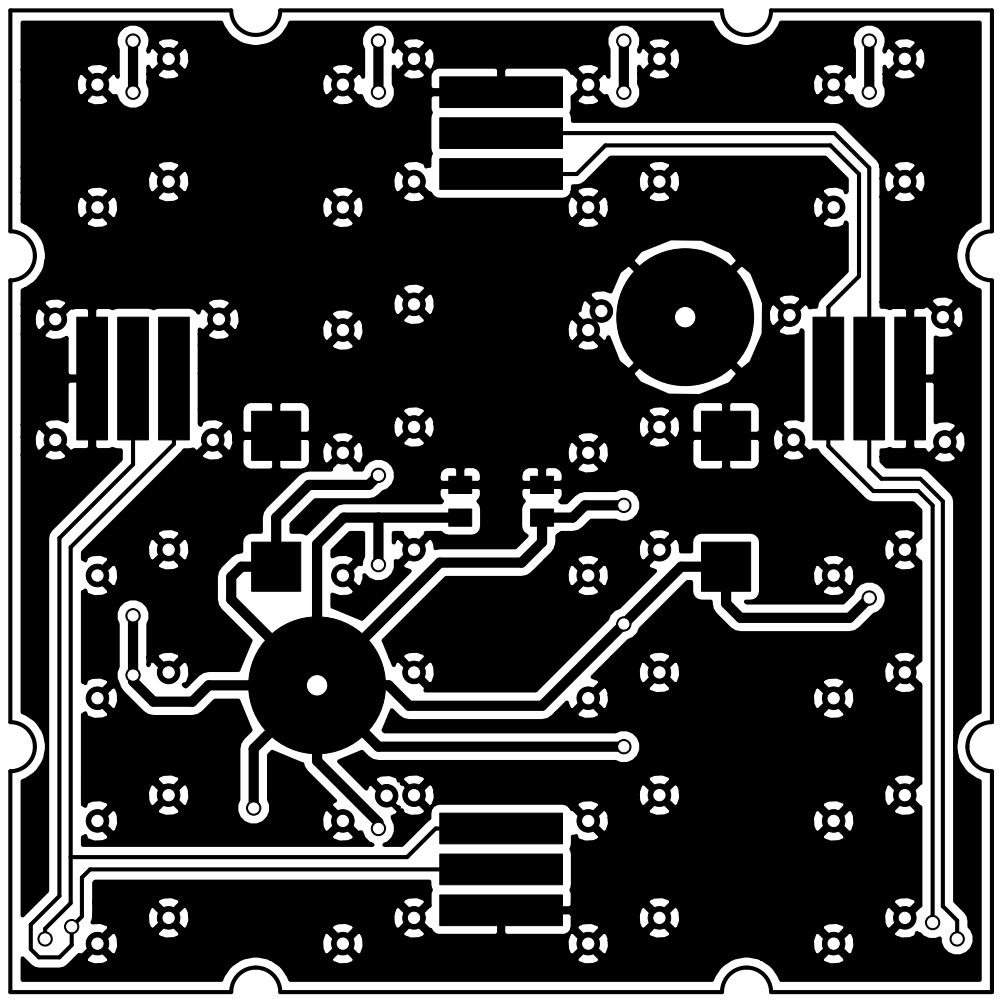
[picture p170: page 1]
