wyolum/ultim8x8/kicad/ultim_8x8_v0/ultim8x8_pdf/ultim8x8-Dwgs.User.pdf

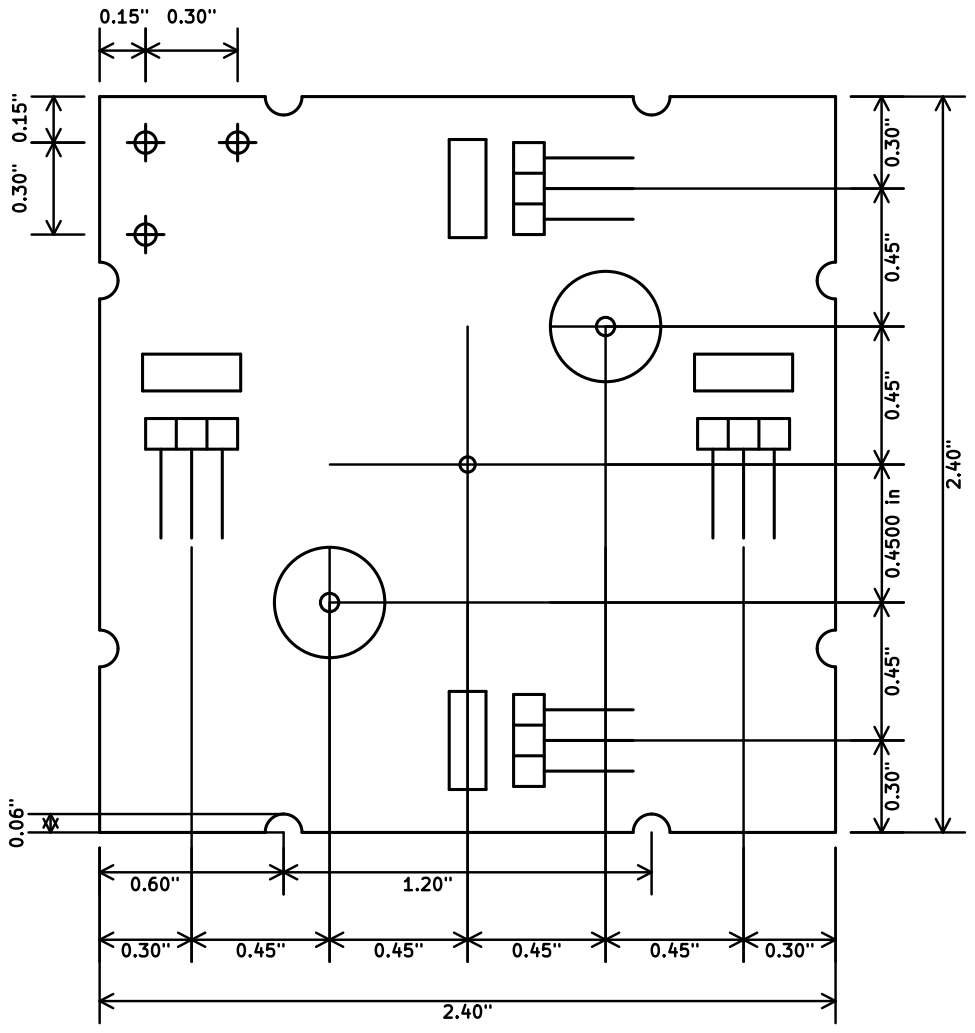
[picture p171: page 1]
