wyolum/ultim8x8/arduino/BLEhat/BLEhat.ino

#include <string.h>
#include <Arduino.h>
#include <SPI.h>

#include <Adafruit_DotStar.h>
#include "Adafruit_BLE.h"
#include "Adafruit_BluefruitLE_SPI.h"

#include "BluefruitConfig.h"
#define DATAPIN    SDA // Ultim8x8
#define CLOCKPIN   SCL // Ultim8x8
#define NUMPIXELS 64

Adafruit_DotStar strip = Adafruit_DotStar(
  NUMPIXELS, DATAPIN, CLOCKPIN, DOTSTAR_BRG);
#define FACTORYRESET_ENABLE         1
#define MINIMUM_FIRMWARE_VERSION    "0.6.6"
#define MODE_LED_BEHAVIOUR          "MODE"
/*=========================================================================*/

/* ...hardware SPI, using SCK/MOSI/MISO hardware SPI pins and then user selected CS/IRQ/RST */
Adafruit_BluefruitLE_SPI ble(BLUEFRUIT_SPI_CS, BLUEFRUIT_SPI_IRQ, BLUEFRUIT_SPI_RST);

/* ...software SPI, using SCK/MOSI/MISO user-defined SPI pins and then user selected CS/IRQ/RST */
//Adafruit_BluefruitLE_SPI ble(BLUEFRUIT_SPI_SCK, BLUEFRUIT_SPI_MISO,
//                             BLUEFRUIT_SPI_MOSI, BLUEFRUIT_SPI_CS,
//                             BLUEFRUIT_SPI_IRQ, BLUEFRUIT_SPI_RST);


// A small helper
void error(const __FlashStringHelper*err) {
  Serial.println(err);
  while (1);
}

// function prototypes over in packetparser.cpp
uint8_t readPacket(Adafruit_BLE *ble, uint16_t timeout);
float parsefloat(uint8_t *buffer);
void printHex(const uint8_t * data, const uint32_t numBytes);

// the packet buffer
extern uint8_t packetbuffer[];

void swipe_clear(){
  for(int i = 0; i < strip.numPixels(); i++){
    strip.setPixelColor(i,0);
    strip.show();
  }
}

void strip_clear(){
  for(int i = 0; i < strip.numPixels(); i++){
    strip.setPixelColor(i,0);
  }
  strip.show();
}

void setPixel(uint8_t row, uint8_t col, uint32_t color){
  int pixel;
  if(row % 2 == 0){
    pixel = 8 * row + col;
  }
  else{
    pixel = 8 * (row + 1) - (col + 1);
  }
  strip.setPixelColor(pixel, color);
}

/**************************************************************************/
/*!
    @brief  Sets up the HW an the BLE module (this function is called
            automatically on startup)
*/
/**************************************************************************/
void setup(void)
{
  delay(500);
  strip.begin();
  strip.setBrightness(8);
  strip.show();
  strip.show();

  Serial.begin(115200);
  Serial.println(F("Adafruit Bluefruit App Controller Example"));
  Serial.println(F("-----------------------------------------"));

  /* Initialise the module */
  Serial.print(F("Initialising the Bluefruit LE module: "));

  if ( !ble.begin(VERBOSE_MODE) )
  {
    error(F("Couldn't find Bluefruit, make sure it's in CoMmanD mode & check wiring?"));
  }
  Serial.println( F("OK!") );

  if ( FACTORYRESET_ENABLE )
  {
    /* Perform a factory reset to make sure everything is in a known state */
    Serial.println(F("Performing a factory reset: "));
    if ( ! ble.factoryReset() ){
      error(F("Couldn't factory reset"));
    }
  }


  /* Disable command echo from Bluefruit */
  ble.echo(false);

  Serial.println("Requesting Bluefruit info:");
  /* Print Bluefruit information */
  ble.info();

  Serial.println(F("Please use Adafruit Bluefruit LE app to connect in Controller mode"));
  Serial.println(F("Then activate/use the sensors, color picker, game controller, etc!"));
  Serial.println();

  ble.verbose(false);  // debug info is a little annoying after this point!

  /* Wait for connection */
  while (! ble.isConnected()) {
      delay(500);
  }

  Serial.println(F("******************************"));

  // LED Activity command is only supported from 0.6.6
  if ( ble.isVersionAtLeast(MINIMUM_FIRMWARE_VERSION) )
  {
    // Change Mode LED Activity
    Serial.println(F("Change LED activity to " MODE_LED_BEHAVIOUR));
    ble.sendCommandCheckOK("AT+HWModeLED=" MODE_LED_BEHAVIOUR);
  }

  // Set Bluefruit to DATA mode
  Serial.println( F("Switching to DATA mode!") );
  ble.setMode(BLUEFRUIT_MODE_DATA);

  Serial.println(F("******************************"));  
}

int lastx =5;
int lasty =5;
int xinc = 1;
int yinc = 1;

uint32_t count = 0;
/**************************************************************************/
/*!
    @brief  Constantly poll for new command or response data
*/
/**************************************************************************/
uint8_t display_mode = 2;
  
void loop(void)
{
  count += 1;
  if(display_mode == 2){
    pong();
  }
  else if(display_mode == 1){
    rainbow();
  }
  else{
    strip_clear();
  }
  
  /* Wait for new data to arrive */
  uint8_t len = readPacket(&ble, BLE_READPACKET_TIMEOUT);
  if (len == 0) return;

  // Color
  if (packetbuffer[1] == 'C') {
    uint8_t red = packetbuffer[2];
    uint8_t green = packetbuffer[3];
    uint8_t blue = packetbuffer[4];
    Serial.print ("RGB #");
    if (red < 0x10) Serial.print("0");
    Serial.print(red, HEX);
    if (green < 0x10) Serial.print("0");
    Serial.print(green, HEX);
    if (blue < 0x10) Serial.print("0");
    Serial.println(blue, HEX);
    display_mode = (red + blue + green > 0);
  }
  
  // Buttons
  if (packetbuffer[1] == 'B') {
    uint8_t buttnum = packetbuffer[2] - '0';
    boolean pressed = packetbuffer[3] - '0';
    Serial.print ("Button "); Serial.print(buttnum);
    if (pressed) {
      Serial.println(" pressed");
    } else {
      Serial.println(" released");
    }
  }

  // GPS Location
  if (packetbuffer[1] == 'L') {
    float lat, lon, alt;
    lat = parsefloat(packetbuffer+2);
    lon = parsefloat(packetbuffer+6);
    alt = parsefloat(packetbuffer+10);
    Serial.print("GPS Location\t");
    Serial.print("Lat: "); Serial.print(lat, 4); // 4 digits of precision!
    Serial.print('\t');
    Serial.print("Lon: "); Serial.print(lon, 4); // 4 digits of precision!
    Serial.print('\t');
    Serial.print(alt, 4); Serial.println(" meters");
  }

  // Accelerometer
  if (packetbuffer[1] == 'A') {
    float x, y, z;
    x = parsefloat(packetbuffer+2);
    y = parsefloat(packetbuffer+6);
    z = parsefloat(packetbuffer+10);
    if (fabs(x) > 3.0)
      xinc = (int)(x/fabs(x));
    else
      xinc = 0;
    if (fabs(y)> 3.0)
      yinc = (int)-(y/fabs(y));
    else
      yinc = 0;
    // strip.setPixelColor((lasty *COLS)+lastx,strip.Color(0,0,0));
    lastx +=  xinc;
    lasty += yinc;
    if (lastx == 8)
      lastx = 7;
    if (lasty == 8)
      lasty = 7;
    if (lastx == -1)
      lastx = 0;
    if (lasty == -1)
      lasty = 0;
    //Serial.print("Setting pixel ");Serial.println((lasty*COLS)+lastx);
    //strip.setPixelColor((lasty * COLS) + lastx, strip.Color(80,0,0));
    strip.show();
  }

  // Magnetometer
  if (packetbuffer[1] == 'M') {
    float x, y, z;
    x = parsefloat(packetbuffer+2);
    y = parsefloat(packetbuffer+6);
    z = parsefloat(packetbuffer+10);
    Serial.print("Mag\t");
    Serial.print(x); Serial.print('\t');
    Serial.print(y); Serial.print('\t');
    Serial.print(z); Serial.println();
  }

  // Gyroscope
  if (packetbuffer[1] == 'G') {
    float x, y, z;
    x = parsefloat(packetbuffer+2);
    y = parsefloat(packetbuffer+6);
    z = parsefloat(packetbuffer+10);
    Serial.print("Gyro\t");
    Serial.print(x); Serial.print('\t');
    Serial.print(y); Serial.print('\t');
    Serial.print(z); Serial.println();
  }

  // Quaternions
  if (packetbuffer[1] == 'Q') {
    float x, y, z, w;
    x = parsefloat(packetbuffer+2);
    y = parsefloat(packetbuffer+6);
    z = parsefloat(packetbuffer+10);
    w = parsefloat(packetbuffer+14);
    Serial.print("Quat\t");
    Serial.print(x); Serial.print('\t');
    Serial.print(y); Serial.print('\t');
    Serial.print(z); Serial.print('\t');
    Serial.print(w); Serial.println();
  }
}

float px = 0;
float py = 0;
float vx = .6;
float vy = 1.03;
void pong(){
  setPixel((int)px, (int)py, 0);
  px += vx;
  py += vy;
  setPixel((int)px, (int)py, Wheel(count % 255));
  strip.show();
  strip.show();
  if(px >= 8 && vx > 0){
    vx *= -1;
  }
  if(px <= 0 && vx < 0){
    vx *= -1;
  }
  if(py >= 8 && vy > 0){
    vy *= -1;
  }
  if(py <= 0 && vy < 0){
    vy *= -1;
  }
}

float cx = 3.5;
float cy = 3.5;

void rainbow() {
  uint16_t row, col;
  for(row=0; row < 8; row++) {
    for(col=0; col < 8; col++) {
      float d = 16 * sqrt((row - cx) * (row - cx) + (col - cy) * (col - cy)) + 3 * count;
      setPixel(row, col, Wheel((int)d & 255));
    }
  }
  setPixel(0, 0, 0);
  setPixel(7, 0, 0);
  setPixel(0, 7, 0);
  setPixel(7, 7, 0);
  strip.show();
}

// Slightly different, this makes the rainbow equally distributed throughout
void rainbowCycle(uint8_t wait) {
  uint16_t i, j;

  for(j=0; j<256*5; j++) { // 5 cycles of all colors on wheel
    for(i=0; i< strip.numPixels(); i++) {
      strip.setPixelColor(i, Wheel(((i * 256 / strip.numPixels()) + j) & 255));
    }
    strip.show();
    delay(wait);
  }
}

//Theatre-style crawling lights.
void theaterChase(uint32_t c, uint8_t wait) {
  for (int j=0; j<10; j++) {  //do 10 cycles of chasing
    for (int q=0; q < 3; q++) {
      for (uint16_t i=0; i < strip.numPixels(); i=i+3) {
        strip.setPixelColor(i+q, c);    //turn every third pixel on
      }
      strip.show();

      delay(wait);

      for (uint16_t i=0; i < strip.numPixels(); i=i+3) {
        strip.setPixelColor(i+q, 0);        //turn every third pixel off
      }
    }
  }
}

//Theatre-style crawling lights with rainbow effect
void theaterChaseRainbow(uint8_t wait) {
  for (int j=0; j < 256; j++) {     // cycle all 256 colors in the wheel
    for (int q=0; q < 3; q++) {
      for (uint16_t i=0; i < strip.numPixels(); i=i+3) {
        strip.setPixelColor(i+q, Wheel( (i+j) % 255));    //turn every third pixel on
      }
      strip.show();

      delay(wait);

      for (uint16_t i=0; i < strip.numPixels(); i=i+3) {
        strip.setPixelColor(i+q, 0);        //turn every third pixel off
      }
    }
  }
}

// Input a value 0 to 255 to get a color value.
// The colours are a transition r - g - b - back to r.
uint32_t Wheel(byte WheelPos) {
  WheelPos = 255 - WheelPos;
  if(WheelPos < 85) {
    return strip.Color(255 - WheelPos * 3, 0, WheelPos * 3);
  }
  if(WheelPos < 170) {
    WheelPos -= 85;
    return strip.Color(0, WheelPos * 3, 255 - WheelPos * 3);
  }
  WheelPos -= 170;
  return strip.Color(WheelPos * 3, 255 - WheelPos * 3, 0);
}
