wyolum/ultim8x8/arduino/BasicHttpClient/BasicHttpClient.ino

/**
   BasicHTTPClient.ino

    Created on: 24.05.2015

*/

#include <Arduino.h>

#include <ESP8266WiFi.h>
#include <ESP8266WiFiMulti.h>

#include <ESP8266HTTPClient.h>
#include <credentials.h>
/* --- credendials.h in arduino library directory ---
char ssid[] = "YOUR_WIFI_HOTSPOT";  // your network SSID (name)
char pass[] = "YOUR_PASSWD";  // your network password
*/

#define USE_SERIAL Serial

ESP8266WiFiMulti WiFiMulti;

void setup() {

  USE_SERIAL.begin(115200);
  // USE_SERIAL.setDebugOutput(true);

  USE_SERIAL.println();
  USE_SERIAL.println();
  USE_SERIAL.println();

  WiFi.mode(WIFI_STA);
  WiFiMulti.addAP(ssid, pass);
  while (WiFi.status() != WL_CONNECTED) {
    delay(500);
    Serial.print(".");
  }
  Serial.println("\nYay, connected!");
  Serial.println(WiFi.localIP());

}

void loop() {
  // wait for WiFi connection
  if ((WiFiMulti.run() == WL_CONNECTED)) {

    HTTPClient http;

    USE_SERIAL.print("[HTTP] begin...\n");
    // configure traged server and url
    //http.begin("https://192.168.1.12/test.html", "7a 9c f4 db 40 d3 62 5a 6e 21 bc 5c cc 66 c8 3e a1 45 59 38"); //HTTPS
    http.begin("http://neverssl.com"); //HTTP

    USE_SERIAL.print("[HTTP] GET...\n");
    // start connection and send HTTP header
    int httpCode = http.GET();

    // httpCode will be negative on error
    if (httpCode > 0) {
      // HTTP header has been send and Server response header has been handled
      USE_SERIAL.printf("[HTTP] GET... code: %d\n", httpCode);

      // file found at server
      if (httpCode == HTTP_CODE_OK) {
        String payload = http.getString();
        USE_SERIAL.println(payload);
      }
    } else {
      USE_SERIAL.printf("[HTTP] GET... failed, error: %s\n", http.errorToString(httpCode).c_str());
    }

    http.end();
  }

  delay(10000);
}
