wyolum/ultim8x8/arduino/BiblioPixelSerialReceiver/MatrixMaps.h

#ifdef ULTIM8x8
#define MatrixWidth 8
#define MatrixHeight 8
uint16_t MatrixMap[MatrixHeight][MatrixWidth] = {
{7,8,23,24,39,40,55,56},
{6,9,22,25,38,41,54,57},
{5,10,21,26,37,42,53,58},
{4,11,20,27,36,43,52,59},
{3,12,19,28,35,44,51,60},
{2,13,18,29,34,45,50,61},
{1,14,17,30,33,46,49,62},
{0,15,16,31,32,47,48,63},
};
#endif

#ifdef ULTIM8x24
#define MatrixWidth 24
#define MatrixHeight 8
uint16_t MatrixMap[MatrixHeight][MatrixWidth] = {
{7,8,23,24,39,40,55,56,71,72,87,88,103,104,119,120,135,136,151,152,167,168,183,184},
{6,9,22,25,38,41,54,57,70,73,86,89,102,105,118,121,134,137,150,153,166,169,182,185},
{5,10,21,26,37,42,53,58,69,74,85,90,101,106,117,122,133,138,149,154,165,170,181,186},
{4,11,20,27,36,43,52,59,68,75,84,91,100,107,116,123,132,139,148,155,164,171,180,187},
{3,12,19,28,35,44,51,60,67,76,83,92,99,108,115,124,131,140,147,156,163,172,179,188},
{2,13,18,29,34,45,50,61,66,77,82,93,98,109,114,125,130,141,146,157,162,173,178,189},
{1,14,17,30,33,46,49,62,65,78,81,94,97,110,113,126,129,142,145,158,161,174,177,190},
{0,15,16,31,32,47,48,63,64,79,80,95,96,111,112,127,128,143,144,159,160,175,176,191},
};
#endif

#ifdef ULTIM24x24
#define MatrixWidth 24
#define MatrixHeight 24
uint16_t MatrixMap[MatrixHeight][MatrixWidth] = {
{7,8,23,24,39,40,55,56,71,72,87,88,103,104,119,120,135,136,151,152,167,168,183,184},
{6,9,22,25,38,41,54,57,70,73,86,89,102,105,118,121,134,137,150,153,166,169,182,185},
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
{891,884,875,868,859,852,843,836,827,820,811,804,795,788,779,772,763,756,747,740,731,724,715,708,699,692,683,676,667,660,651,644,635,628,619,612,603,596,587,580,571,564,555,548,539,532,523,516,507,500,491,484,475,468,459,452},
{890,885,874,869,858,853,842,837,826,821,810,805,794,789,778,773,762,757,746,741,730,725,714,709,698,693,682,677,666,661,650,645,634,629,618,613,602,597,586,581,570,565,554,549,538,533,522,517,506,501,490,485,474,469,458,453},
{889,886,873,870,857,854,841,838,825,822,809,806,793,790,777,774,761,758,745,742,729,726,713,710,697,694,681,678,665,662,649,646,633,630,617,614,601,598,585,582,569,566,553,550,537,534,521,518,505,502,489,486,473,470,457,454},
{888,887,872,871,856,855,840,839,824,823,808,807,792,791,776,775,760,759,744,743,728,727,712,711,696,695,680,679,664,663,648,647,632,631,616,615,600,599,584,583,568,567,552,551,536,535,520,519,504,503,488,487,472,471,456,455},
};
#endif
