wyolum/ultim8x8/arduino/IO-Panel/config.h

/************************ Adafruit IO Config *******************************/

// visit io.adafruit.com if you need to create an account,
// or if you need your Adafruit IO key.
#define IO_USERNAME    "yourusername"
#define IO_KEY         "youraoikey"

/******************************* WIFI **************************************/

// the AdafruitIO_WiFi client will work with the following boards:
//   - HUZZAH ESP8266 Breakout -> https://www.adafruit.com/products/2471
//   - Feather HUZZAH ESP8266 -> https://www.adafruit.com/products/2821
//   - Feather M0 WiFi -> https://www.adafruit.com/products/3010
//   - Feather WICED -> https://www.adafruit.com/products/3056

#define WIFI_SSID       "youssid"
#define WIFI_PASS       "yourpasswd"

// comment out the following two lines if you are using fona or ethernet
#include "AdafruitIO_WiFi.h"
AdafruitIO_WiFi io(IO_USERNAME, IO_KEY, WIFI_SSID, WIFI_PASS);


/******************************* FONA **************************************/

// the AdafruitIO_FONA client will work with the following boards:
//   - Feather 32u4 FONA -> https://www.adafruit.com/product/3027

// uncomment the following two lines for 32u4 FONA,
// and comment out the AdafruitIO_WiFi client in the WIFI section
// #include "AdafruitIO_FONA.h"
// AdafruitIO_FONA io(IO_USERNAME, IO_KEY);


/**************************** ETHERNET ************************************/

// the AdafruitIO_Ethernet client will work with the following boards:
//   - Ethernet FeatherWing -> https://www.adafruit.com/products/3201

// uncomment the following two lines for ethernet,
// and comment out the AdafruitIO_WiFi client in the WIFI section
// #include "AdafruitIO_Ethernet.h"
// AdafruitIO_Ethernet io(IO_USERNAME, IO_KEY);
