wyolum/ultim8x8/arduino/TakeANumber/Fields.h

/*
   ESP8266 + FastLED + IR Remote: https://github.com/jasoncoon/esp8266-fastled-webserver
   Copyright (C) 2016 Jason Coon

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
   You should have received a copy of the GNU General Public License
   along with this program.  If not, see <http://www.gnu.org/licenses/>.
*/

uint8_t power = 1;
uint8_t display_clock = 1;
uint8_t alarm = 1;
uint8_t brightness = brightnessMap[brightnessIndex];
int8_t timezone = -5;
uint32_t take_a_number = 17;
uint8_t alarm_hour, alarm_minute;

//String setPower(String value) {
//  power = value.toInt();
//  if(power < 0) power = 0;
//  else if (power > 1) power = 1;
//  return String(power);
//}

String getPower() {
  return String(power);
}

String getDisplayClock() {
  return String(display_clock);
}

String getAlarm() {
  return String(alarm);
}

String getTakeANumber() {
  return String(take_a_number);
}

String getBrightness() {
  return String(brightness);
}

String getPattern() {
  return String(currentPatternIndex);
}

String getPatterns() {
  String json = "";

  for (uint8_t i = 0; i < patternCount; i++) {
    json += "\"" + patterns[i].name + "\"";
    if (i < patternCount - 1)
      json += ",";
  }

  return json;
}

String getPalette() {
  return String(currentPaletteIndex);
}

String getPalettes() {
  String json = "";

  for (uint8_t i = 0; i < paletteCount; i++) {
    json += "\"" + paletteNames[i] + "\"";
    if (i < paletteCount - 1)
      json += ",";
  }

  return json;
}

String getAutoplay() {
  return String(autoplay);
}

String getAutoplayDuration() {
  return String(autoplayDuration);
}

String getSolidColor() {
  return String(solidColor.r) + "," + String(solidColor.g) + "," + String(solidColor.b);
}

String getCooling() {
  return String(cooling);
}

String getSparking() {
  return String(sparking);
}

String getSpeed() {
  return String(speed);
}

String getTwinkleSpeed() {
  return String(twinkleSpeed);
}

String getTwinkleDensity() {
  return String(twinkleDensity);
}

FieldList fields = {
  { "power", "Power", BooleanFieldType, 0, 1, getPower },
  //{ "display_clock", "Clock", BooleanFieldType, 0, 1, getDisplayClock },
  { "take_a_number", "Now Serving:", NumberFieldType, 0, 99, getTakeANumber },
  {    "brightness",    "Brightness", NumberFieldType, 1, 255, getBrightness },
};

uint8_t fieldCount = ARRAY_SIZE(fields);
