wyolum/ultim8x8/arduino/Kandy2/kandy_commands.h

const uint8_t KANDY_START           = 1;
const uint8_t KANDY_STOP            = 2;
const uint8_t KANDY_INC_HOUR        = 3;
const uint8_t KANDY_DEC_HOUR        = 4;
const uint8_t KANDY_INC_MIN         = 5;
const uint8_t KANDY_DEC_MIN         = 6;
const uint8_t KANDY_INC_SEC         = 7;
const uint8_t KANDY_DEC_SEC         = 8;
const uint8_t KANDY_ZERO_SEC        = 9;
const uint8_t KANDY_INC_CD_HOUR     = 10;
const uint8_t KANDY_DEC_CD_HOUR     = 11;
const uint8_t KANDY_INC_CD_MIN      = 12;
const uint8_t KANDY_DEC_CD_MIN      = 13;
const uint8_t KANDY_INC_CD_SEC      = 14;
const uint8_t KANDY_DEC_CD_SEC      = 15;
const uint8_t KANDY_INC_BRIGHTNESS  = 16;
const uint8_t KANDY_DEC_BRIGHTNESS  = 17;
const uint8_t KANDY_INC_MODE        = 18;
const uint8_t KANDY_DEC_MODE        = 19;
const uint8_t KANDY_SET_TO_MIDNIGHT = 20;
const uint8_t KANDY_INC_RACE_HOUR   = 21;
const uint8_t KANDY_DEC_RACE_HOUR   = 22;
const uint8_t KANDY_INC_RACE_MIN    = 23;
const uint8_t KANDY_DEC_RACE_MIN    = 24;
const uint8_t KANDY_INC_RACE_SEC    = 25;
const uint8_t KANDY_DEC_RACE_SEC    = 26;
const uint8_t KANDY_INC_N_WAVE      = 27;
const uint8_t KANDY_DEC_N_WAVE      = 28;
const uint8_t KANDY_INC_WAVE_SEP    = 29;
const uint8_t KANDY_DEC_WAVE_SEP    = 30;
const uint8_t KANDY_RACE_STOP       = 31;

const uint8_t KANDY_MAX_COMMAND     = 31;
const uint16_t MAX_WAVE_SEP         = 9999;
