wyolum/ultim8x8/arduino/Kandy2/kandy_commands.py

START           = chr(1)
STOP            = chr(2)
INC_HOUR        = chr(3)
DEC_HOUR        = chr(4)
INC_MIN         = chr(5)
DEC_MIN         = chr(6)
INC_SEC         = chr(7)
DEC_SEC         = chr(8)
ZERO_SEC        = chr(9)
INC_CD_HOUR     = chr(10)
DEC_CD_HOUR     = chr(11)
INC_CD_MIN      = chr(12)
DEC_CD_MIN      = chr(13)
INC_CD_SEC      = chr(14)
DEC_CD_SEC      = chr(15)
INC_BRIGHTNESS  = chr(16)
DEC_BRIGHTNESS  = chr(17)
INC_MODE        = chr(18)
DEC_MODE        = chr(19)
SET_TO_MIDNIGHT = chr(20)
INC_RACE_HOUR   = chr(21)
DEC_RACE_HOUR   = chr(22)
INC_RACE_MIN    = chr(23)
DEC_RACE_MIN    = chr(24)
INC_RACE_SEC    = chr(25)
DEC_RACE_SEC    = chr(26)
INC_N_WAVE      = chr(27);
DEC_N_WAVE      = chr(28);
INC_WAVE_SEP    = chr(29);
DEC_WAVE_SEP    = chr(30);
