wyolum/ultim8x8/arduino/BiblioPixelSerialReceiver/test8x24.py

from bibliopixel.drivers.serial_driver import DriverSerial, LEDTYPE
from bibliopixel import LEDMatrix, log
from BiblioPixelAnimations.matrix.bloom import Bloom
log.setLogLevel(log.DEBUG)

driver = DriverSerial(LEDTYPE.GENERIC, 64*3, hardwareID="16C0:0483", dev="/dev/ttyACM0")
led = LEDMatrix(driver, width=24, height=8)

try:
    anim = Bloom(led, dir=True)
    anim.run(amt=1, fps=15)
except:
    raise
    led.all_off()
    led.update()
